anhembedded/PCS_HMI/Doc/bv h.Anh/an/1.PNG

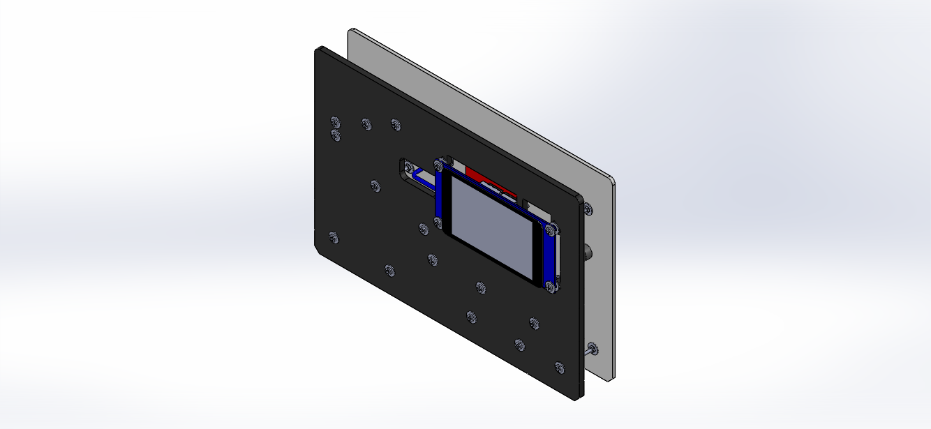
Doc/bv h.Anh/an/1.PNG
