anhembedded/PCS_HMI/Doc/bv h.Anh/an/2.PNG

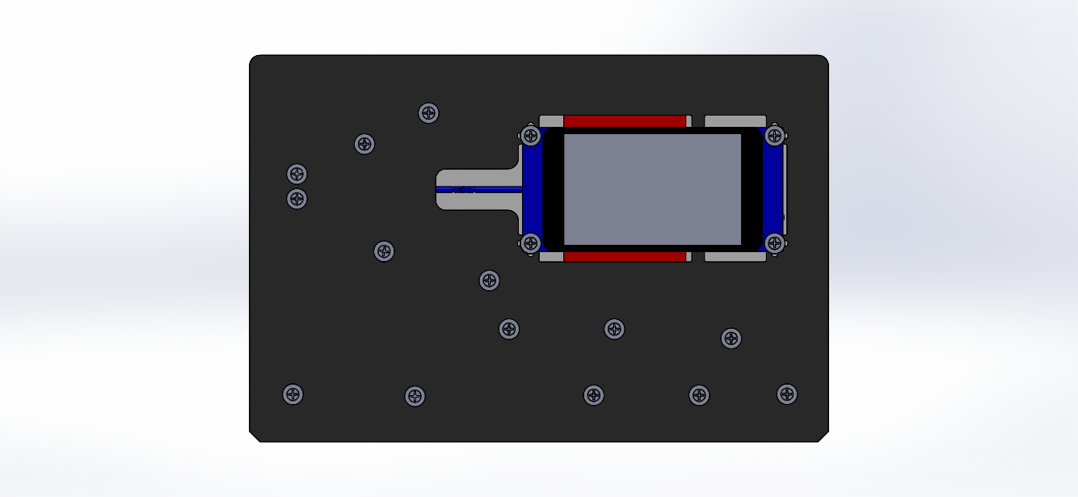
Doc/bv h.Anh/an/2.PNG
