anhembedded/PCS_HMI/Doc/bv h.Anh/an/3.PNG

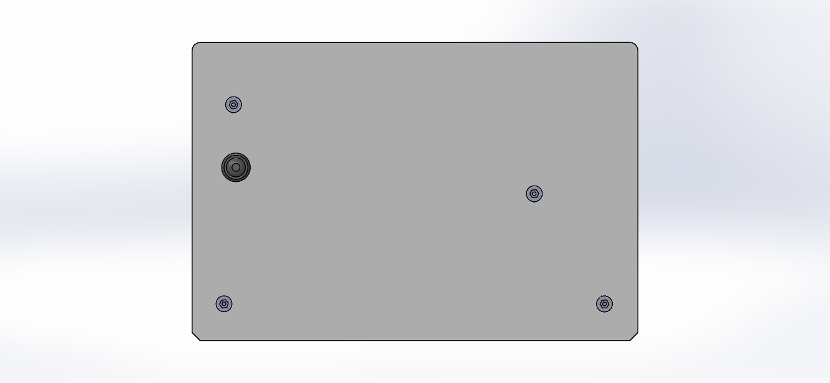
Doc/bv h.Anh/an/3.PNG
