anhembedded/PCS_HMI/Doc/bv h.Anh/an/4.PNG

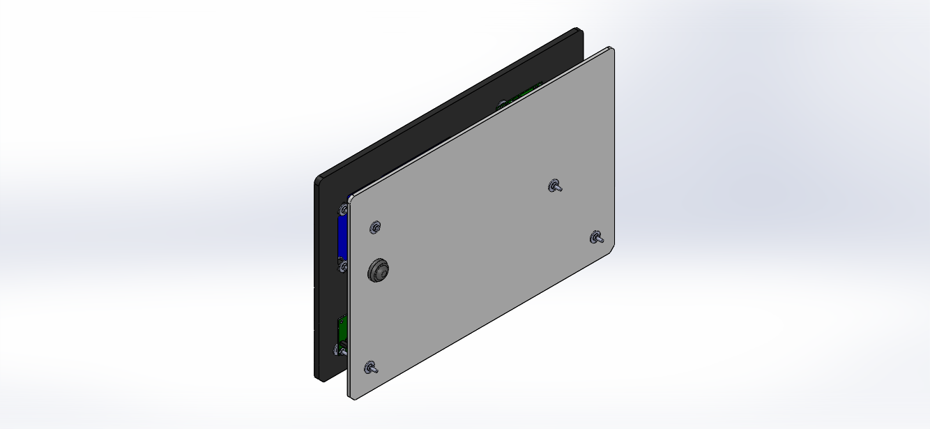
Doc/bv h.Anh/an/4.PNG
