anhembedded/PCS_HMI/Doc/bv h.Anh/an/6.PNG

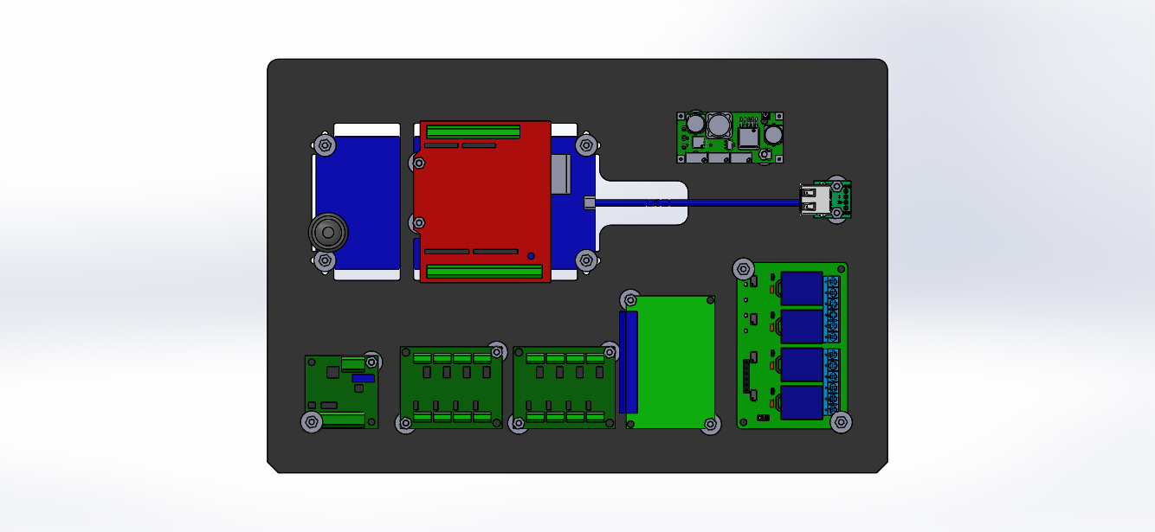
Doc/bv h.Anh/an/6.PNG
