anhembedded/PCS_HMI/Doc/bv h.Anh/arduino-uno-screw-shield-1.snapshot.9/Arduino_Uno_Screw_Shield_2020-Apr-12_04-04-14PM-000_CustomizedView19579382363.png

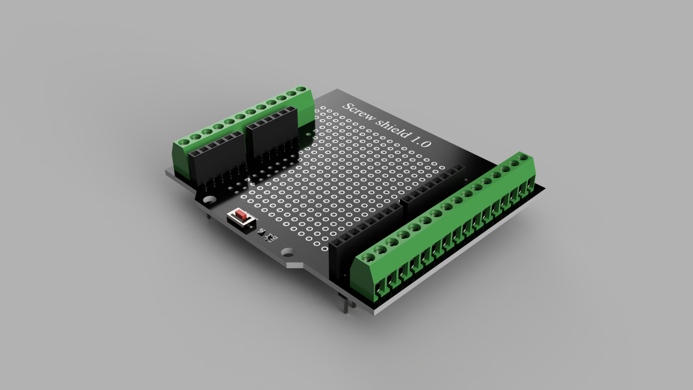
Doc/bv h.Anh/arduino-uno-screw-shield-1.snapshot.9/Arduino_Uno_Screw_Shield_2020-Apr-12_04-04-14PM-000_CustomizedView19579382363.png
