anhembedded/PCS_HMI/Doc/bv h.Anh/arduino-uno-screw-shield-1.snapshot.9/ScrewShield.jpg

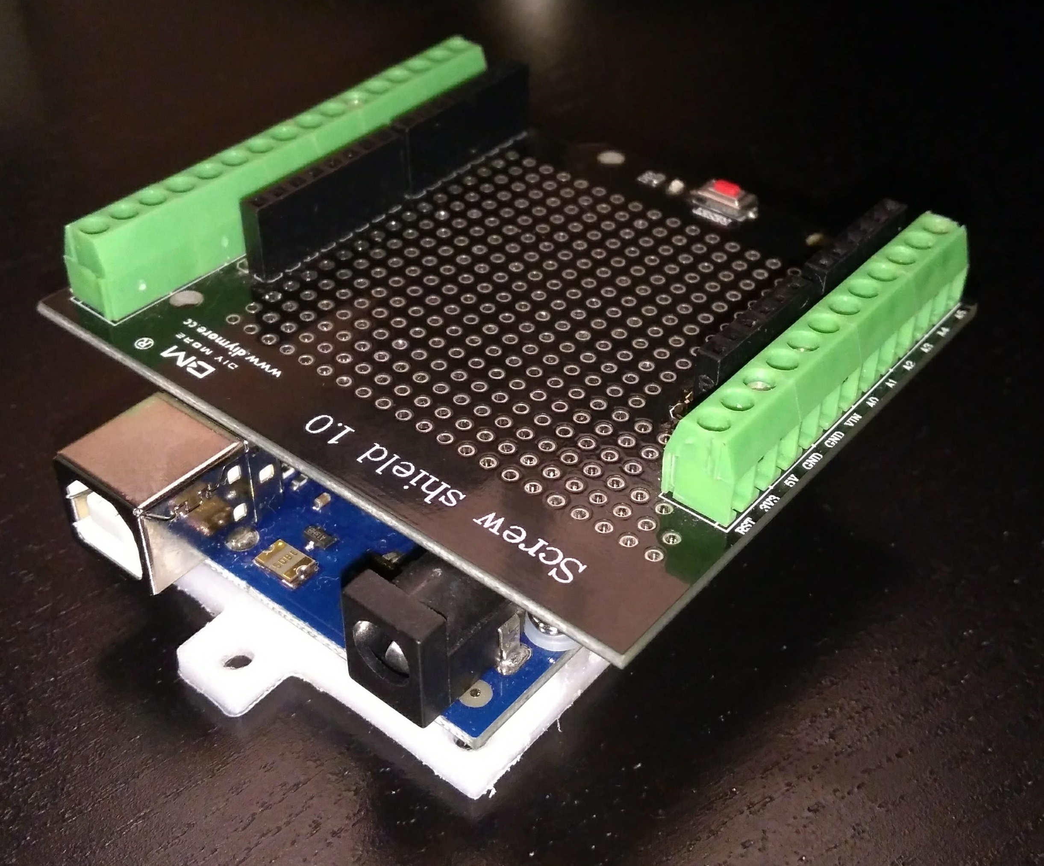
Doc/bv h.Anh/arduino-uno-screw-shield-1.snapshot.9/ScrewShield.jpg
