anhembedded/PCS_HMI/HMI_FPAC_BACKEND/TouchGFX/assets/images/__generated/alternate_theme_images_backgrounds_480x272_gradient_dark.png

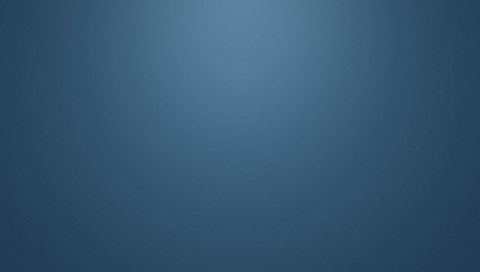
HMI_FPAC_BACKEND/TouchGFX/assets/images/__generated/alternate_theme_images_backgrounds_480x272_gradient_dark.png
