anhembedded/PCS_HMI/HMI_FPAC_BACKEND/TouchGFX/assets/images/__generated/alternate_theme_images_containers_large_wide_outlined_dark.png

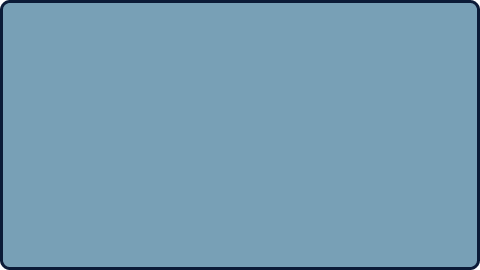
HMI_FPAC_BACKEND/TouchGFX/assets/images/__generated/alternate_theme_images_containers_large_wide_outlined_dark.png
