anhembedded/PCS_HMI/HMI_FPAC_BACKEND/TouchGFX/assets/images/__generated/alternate_theme_images_effects_800x480_shade_right_light.png

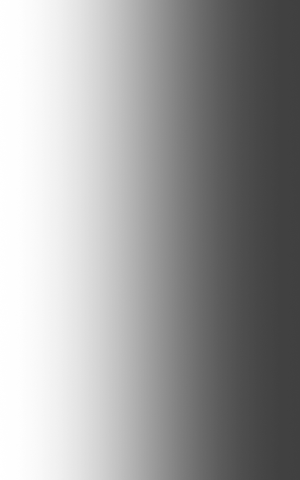
HMI_FPAC_BACKEND/TouchGFX/assets/images/__generated/alternate_theme_images_effects_800x480_shade_right_light.png
