anhembedded/PCS_HMI/Doc/bv h.Anh/mica/mica den 7mm.dxf

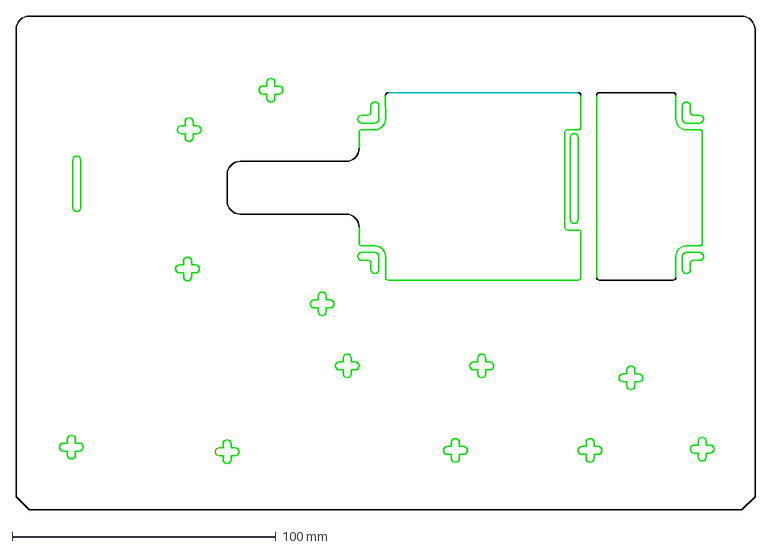
[picture p83: CAD file, 2023-07-13]
Doc/bv h.Anh/mica/mica den 7mm.dxf
280.0 x 187.0 mm
