anhembedded/PCS_HMI/Doc/bv h.Anh/ban dien/de.SLDPRT

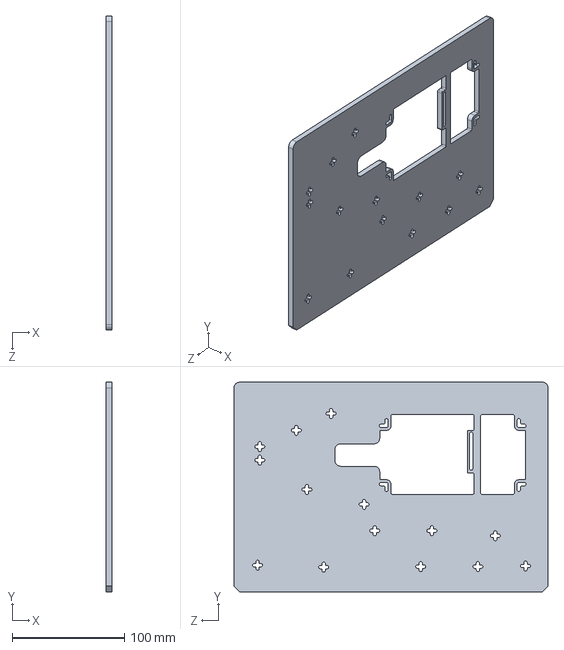
[picture p84: CAD file, 2023-07-13]
Doc/bv h.Anh/ban dien/de.SLDPRT
5.00 x 187.0 x 280.0 mm
