anhembedded/PCS_HMI/Doc/bv h.Anh/ban dien/tam lot.SLDPRT

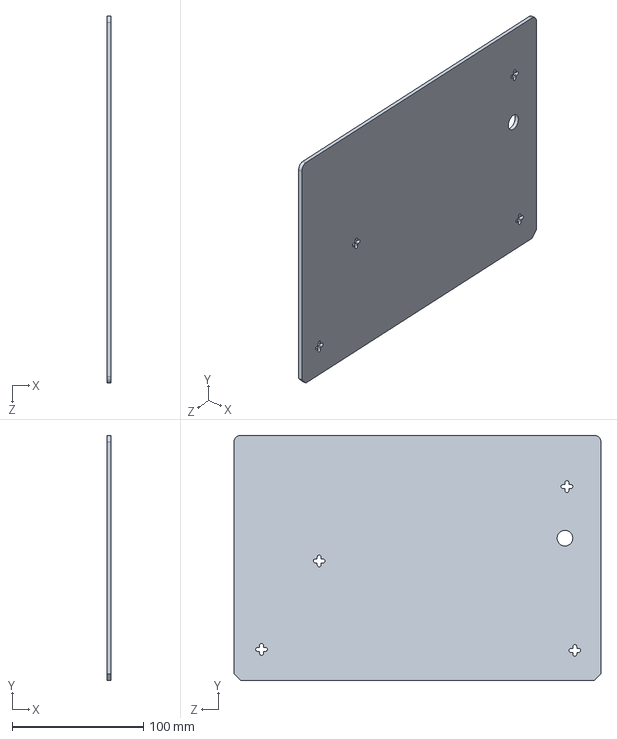
[picture p85: CAD file, 2023-07-13]
Doc/bv h.Anh/ban dien/tam lot.SLDPRT
3.00 x 187.0 x 280.0 mm
