anhembedded/PCS_HMI/Doc/bv h.Anh/ban dien/dai oc m3.SLDPRT

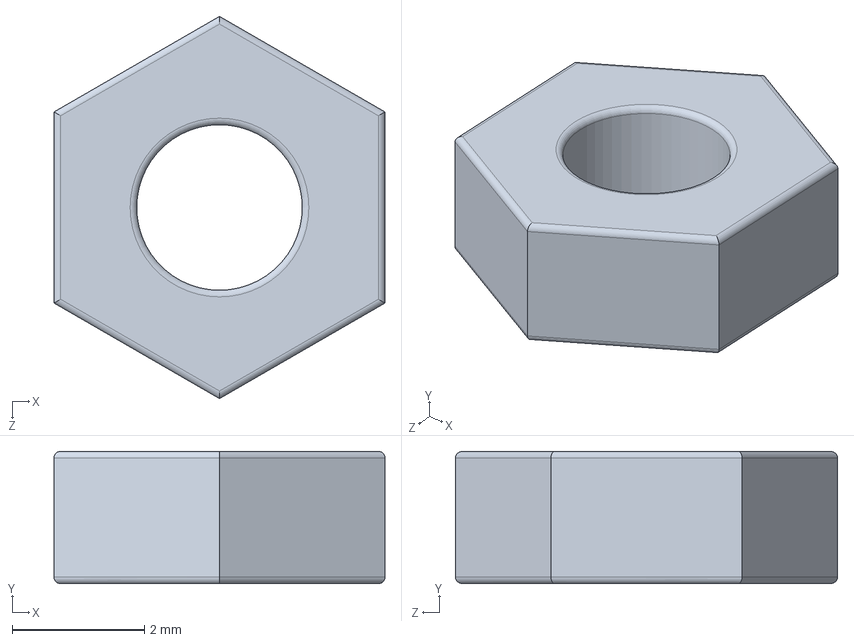
[picture p86: CAD file, 2023-07-13]
Doc/bv h.Anh/ban dien/dai oc m3.SLDPRT
5.00 x 2.00 x 5.77 mm
