anhembedded/PCS_HMI/Doc/bv h.Anh/ban dien/man hinh.SLDPRT

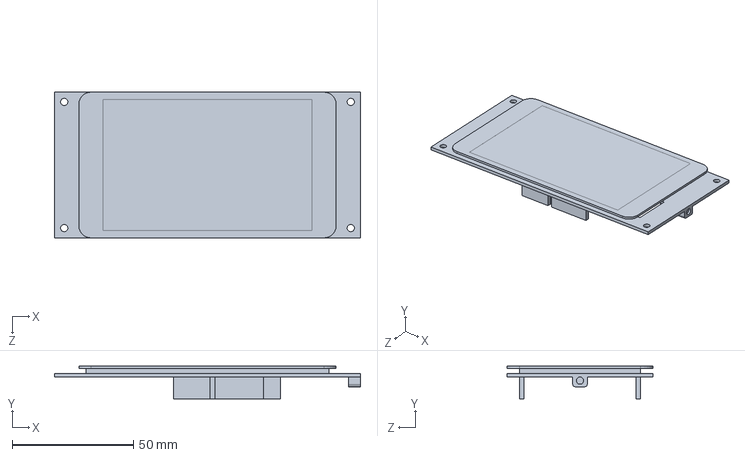
[picture p87: CAD file, 2023-07-13]
Doc/bv h.Anh/ban dien/man hinh.SLDPRT
126.0 x 13.5 x 60.0 mm
