anhembedded/PCS_HMI/Doc/bv h.Anh/ban dien/1.SLDPRT

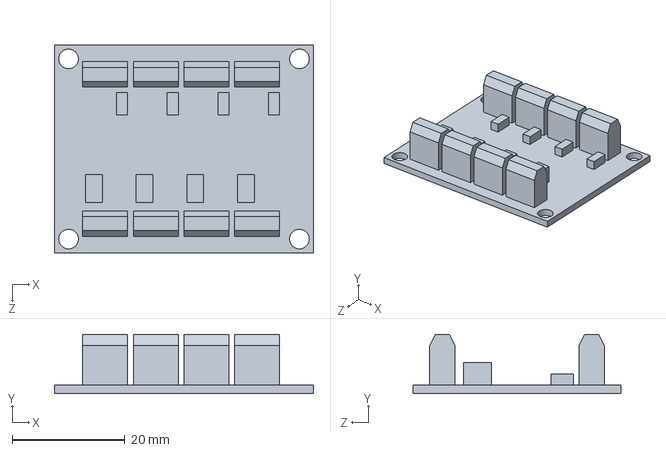
[picture p88: CAD file, 2023-07-13]
Doc/bv h.Anh/ban dien/1.SLDPRT
46.0 x 10.5 x 37.0 mm
