anhembedded/PCS_HMI/Doc/bv h.Anh/ban dien/New folder/Relay002.sldprt

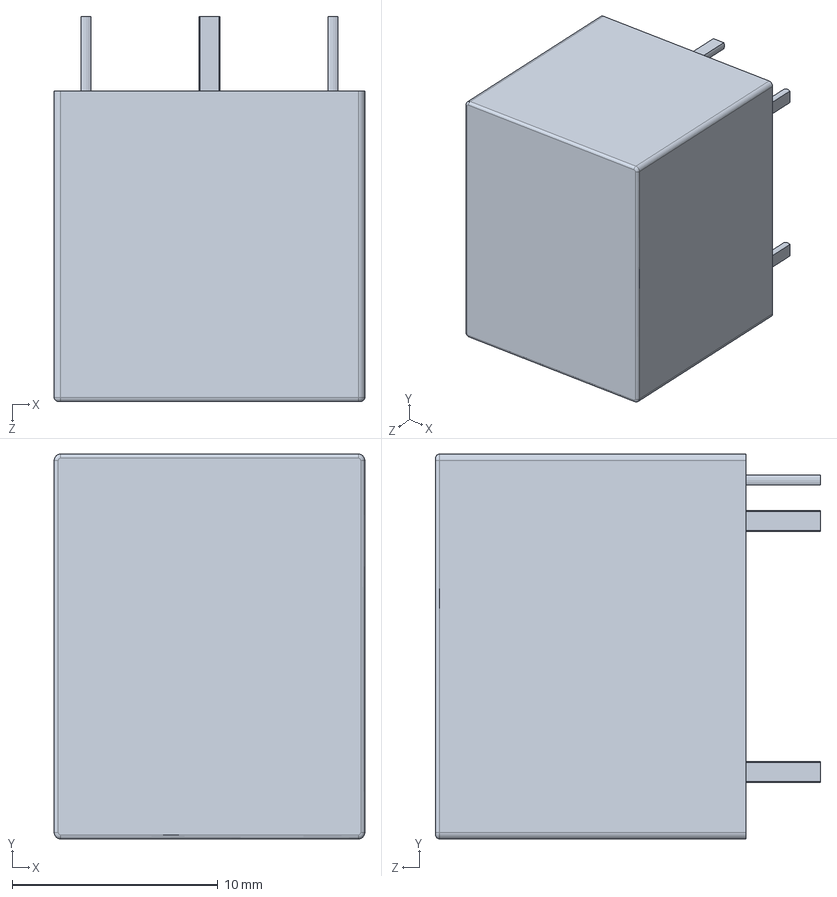
[picture p89: CAD file, 2023-07-13]
Doc/bv h.Anh/ban dien/New folder/Relay002.sldprt
15.1 x 18.7 x 18.7 mm
