anhembedded/PCS_HMI/Doc/bv h.Anh/ban dien/day cap.SLDPRT

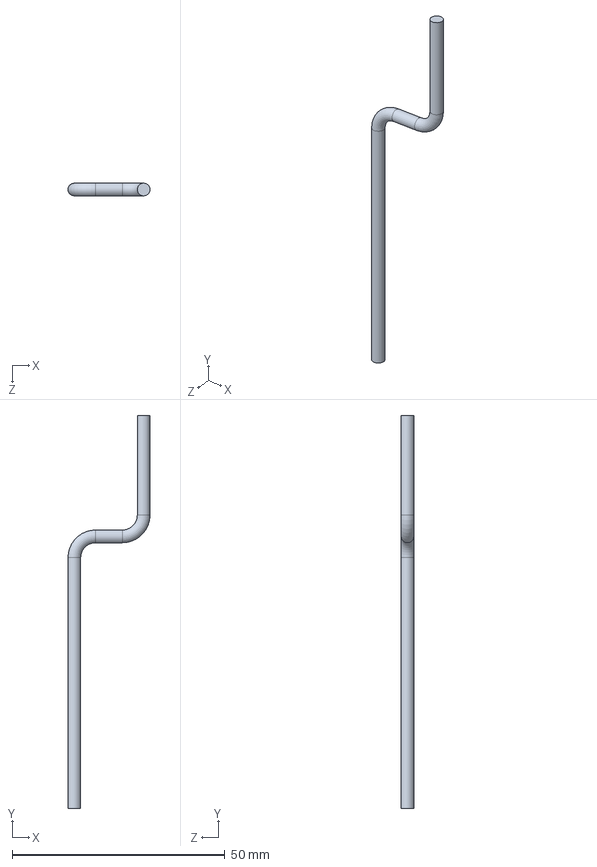
[picture p90: CAD file, 2023-07-13]
Doc/bv h.Anh/ban dien/day cap.SLDPRT
19.3 x 92.4 x 3.00 mm
