anhembedded/PCS_HMI/Doc/bv h.Anh/ban dien/m3.SLDPRT

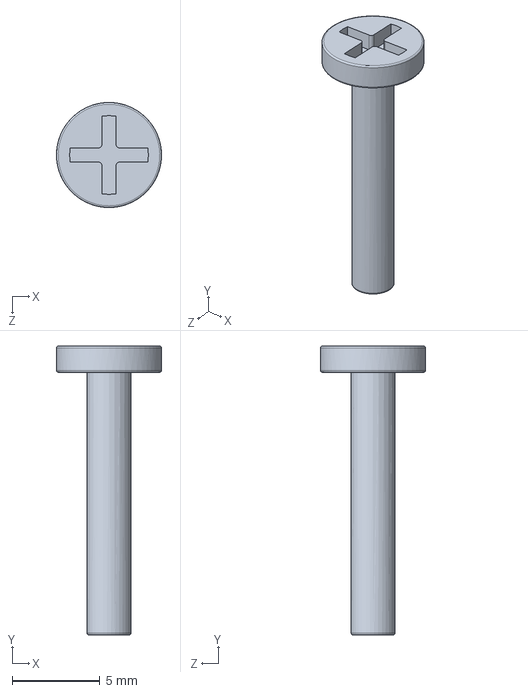
[picture p91: CAD file, 2023-07-13]
Doc/bv h.Anh/ban dien/m3.SLDPRT
6.00 x 16.5 x 6.00 mm
