anhembedded/PCS_HMI/Doc/bv h.Anh/ban dien/3.SLDPRT

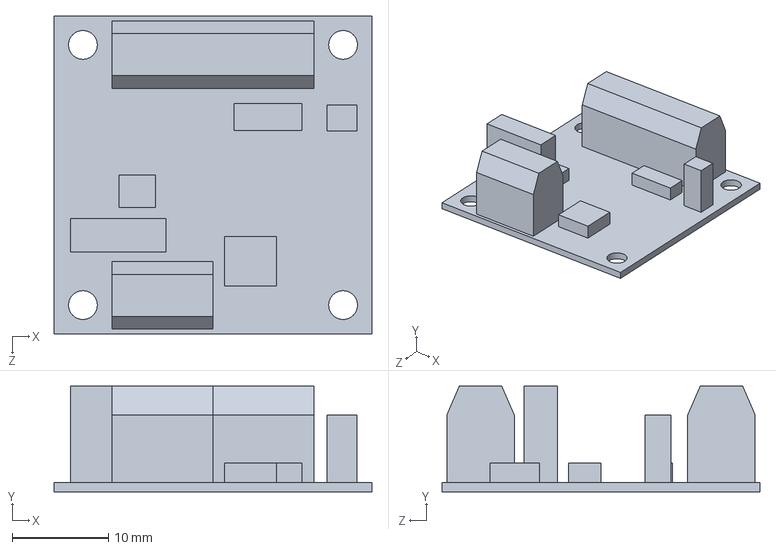
[picture p92: CAD file, 2023-07-13]
Doc/bv h.Anh/ban dien/3.SLDPRT
33.0 x 11.0 x 33.0 mm
