anhembedded/PCS_HMI/Doc/bv h.Anh/ban dien/PCB^DC-DC.sldprt

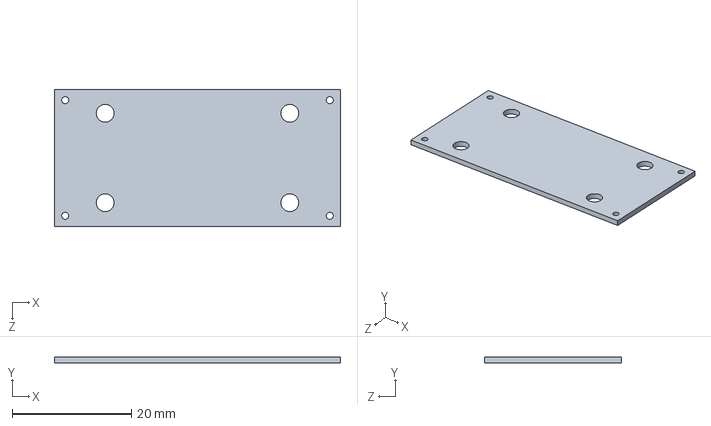
[picture p93: CAD file, 2023-07-13]
Doc/bv h.Anh/ban dien/PCB^DC-DC.sldprt
48.0 x 1.00 x 23.0 mm
