anhembedded/PCS_HMI/Doc/bv h.Anh/ban dien/usb.SLDPRT

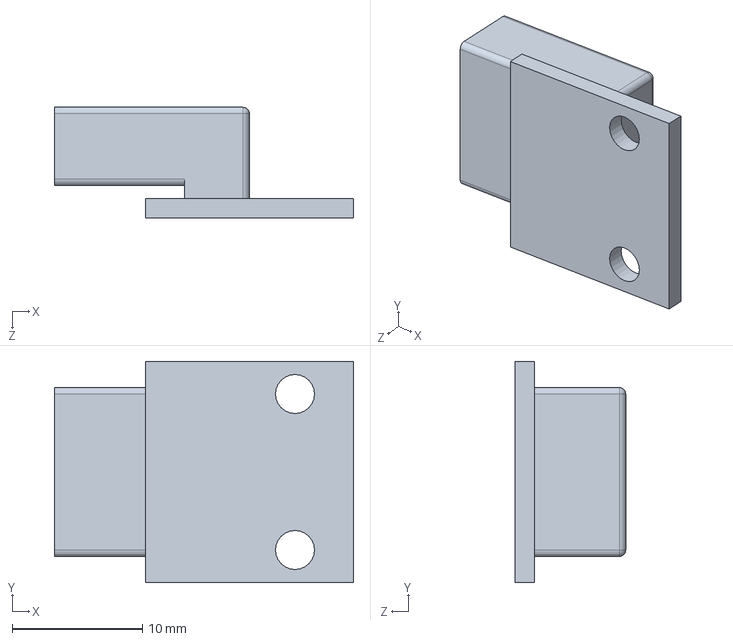
[picture p94: CAD file, 2023-07-13]
Doc/bv h.Anh/ban dien/usb.SLDPRT
23.0 x 17.0 x 8.50 mm
