anhembedded/PCS_HMI/Doc/2d model.pdf

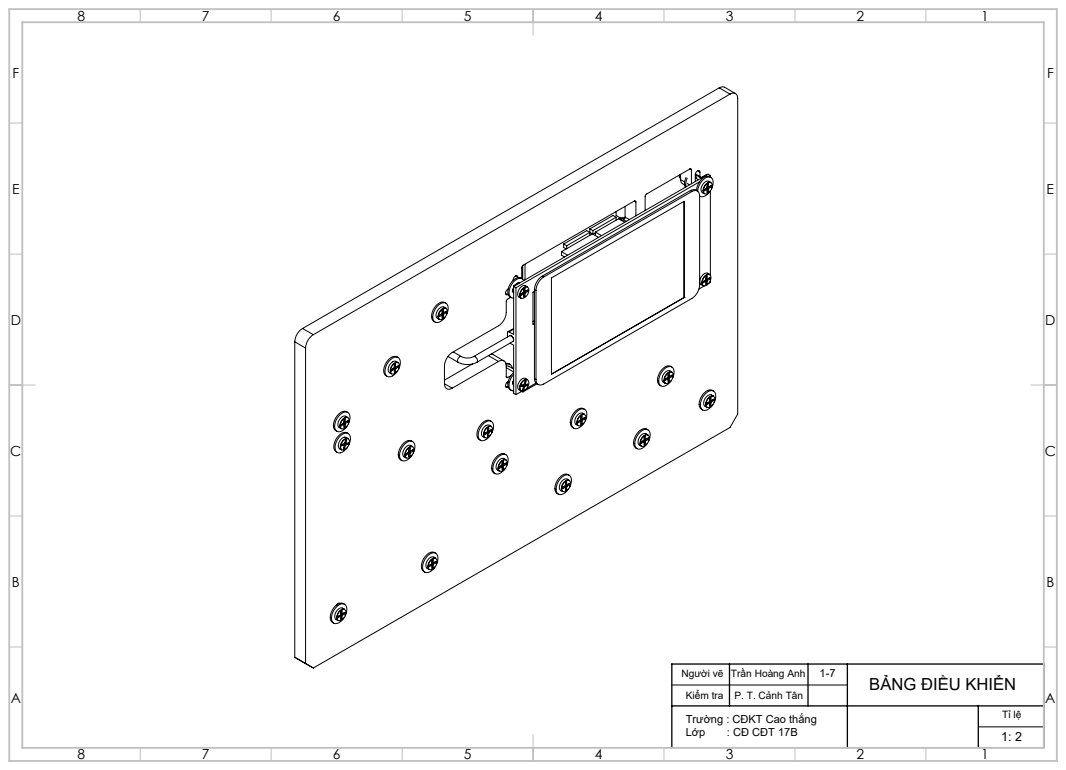
[picture p96: page 1]

Người vẽ Kiểm tra | Trần Hoàng Anh P. T. Cảnh Tân | 1-7 | BẢNG ĐIỀU KHIỂN

Trường : CĐKT Cao thắng Lớp : CĐ CĐT 17B | | Tỉ lệ 1: 2

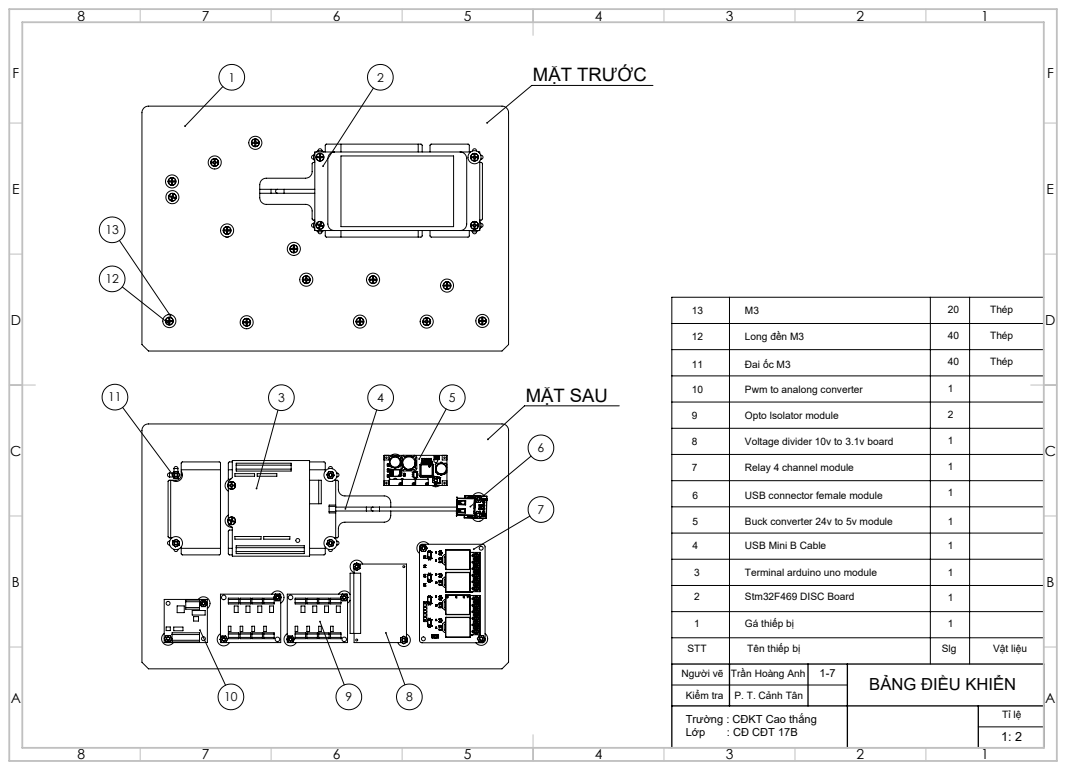
[picture p97: page 2]
MẶT SAU; MẶT TRƯỚC; Lớp; : CĐ CĐT 17B

13 | M3 | 20 | Thép
12 | Long đền M3 | 40 | Thép
11 | Đai ốc M3 | 40 | Thép
10 | Pwm to analong converter | 1
9 | Opto lsolator module | 2
8 | Voltage divider 10v to 3.1v board | 1
7 | Relay 4 channel module | 1
6 | USB connector female module | 1

5 | Buck converter 24v to 5v module | 1
4 | USB Mini B Cable | 1

3 | Terminal arduino uno module | 1
2 | Stm32F469 DISC Board | 1

1 | Gá thiếp bị | 1
STT | Tên thiếp bị | Slg | Vật liệu
Người vẽ | Trần Hoàng Anh | 1-7 | BẢNG ĐIỀU KHIỂN
Kiểm tra | P. T. Cảnh Tân

Trường : CĐKT Cao thắng

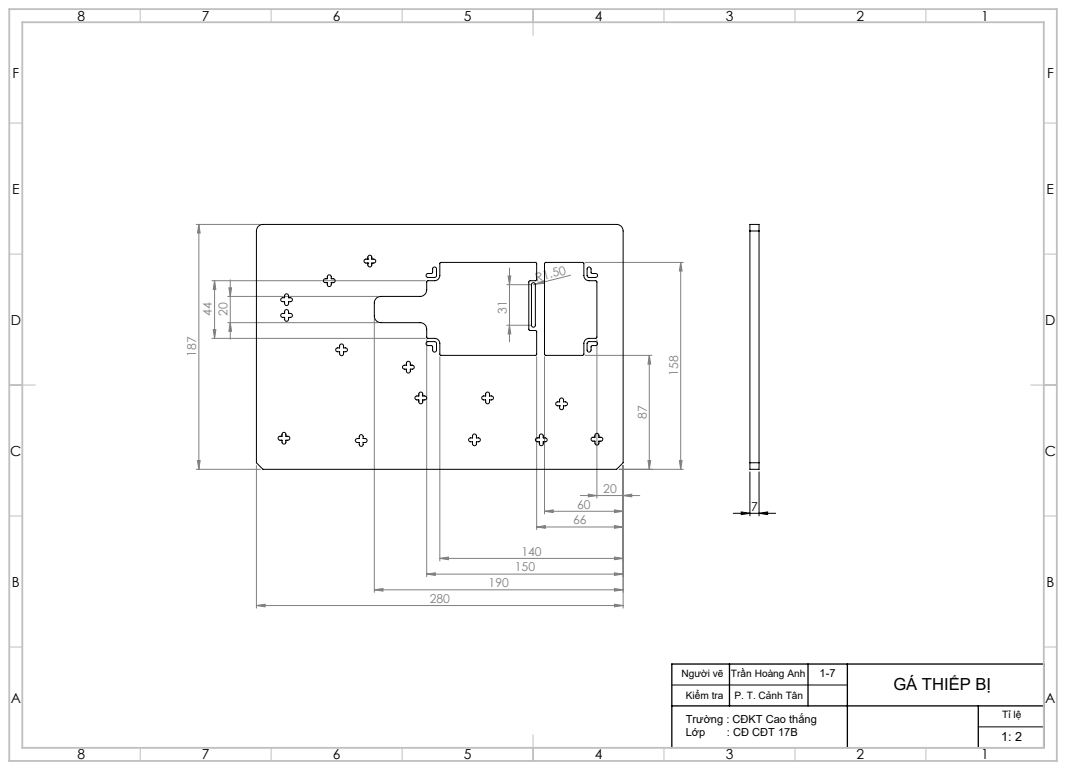
[picture p98: page 3]

Người vẽ Kiểm tra | Trần Hoàng Anh P. T. Cảnh Tân | 1-7 | GÁ THIẾP BỊ

Trường : CĐKT Cao thắng Lớp : CĐ CĐT 17B | | Tỉ lệ 1: 2

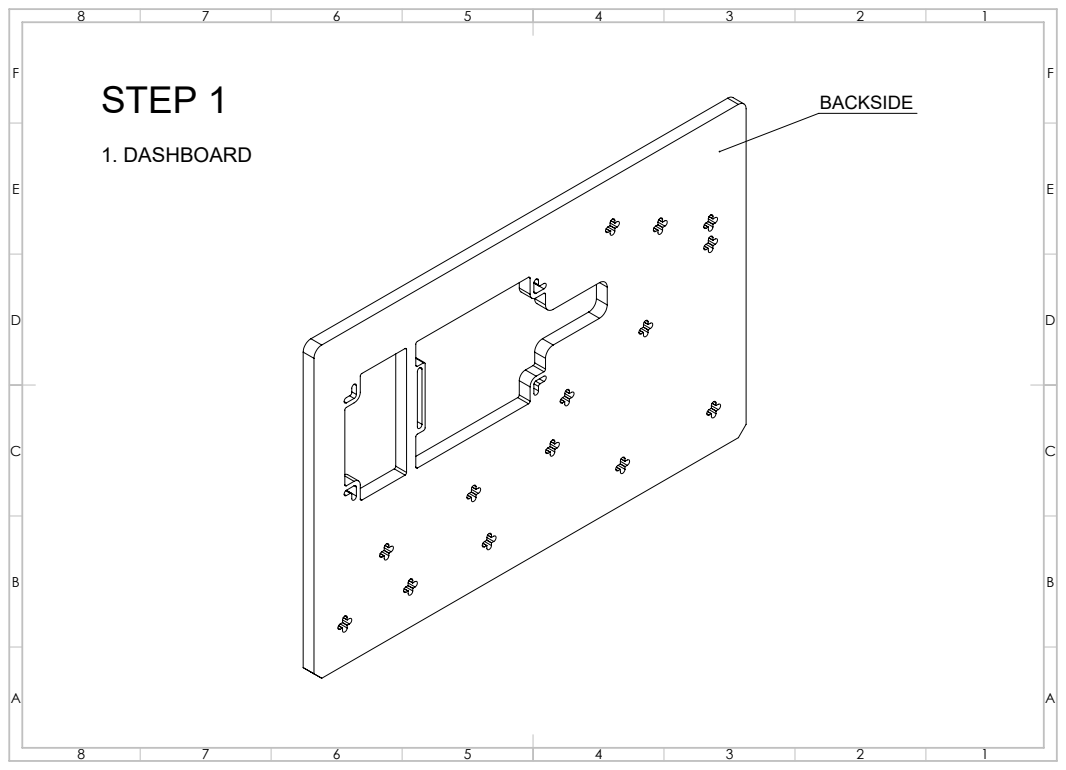
[picture p99: page 4]
STEP 1 BACKSIDE; 1. DASHBOARD

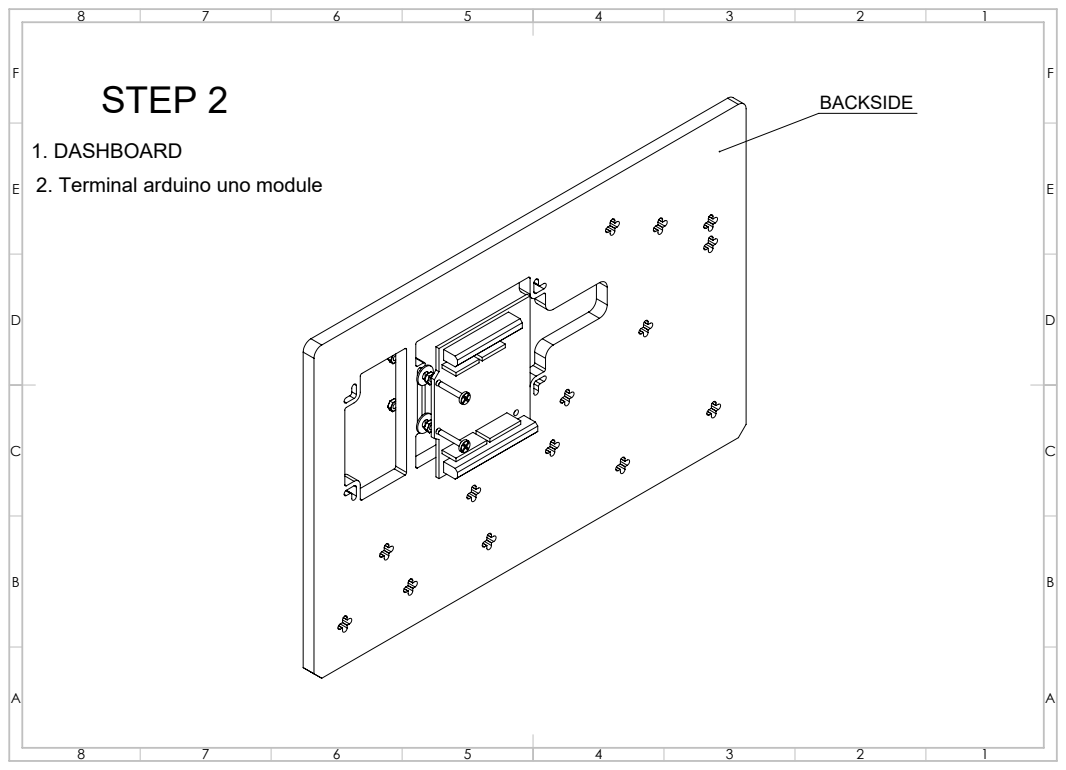
[picture p100: page 5]
STEP 2 BACKSIDE

1. DASHBOARD
2. Terminal arduino uno module

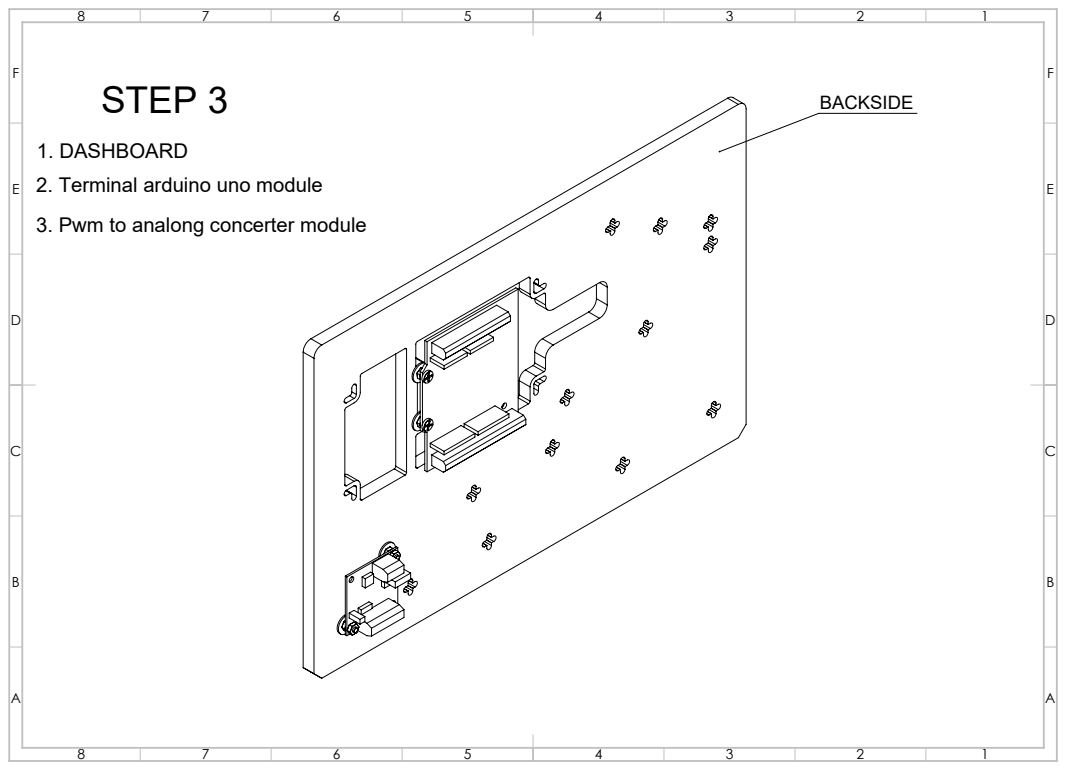
[picture p101: page 6]
STEP 3 BACKSIDE

1. DASHBOARD
2. Terminal arduino uno module
3. Pwm to analong concerter module

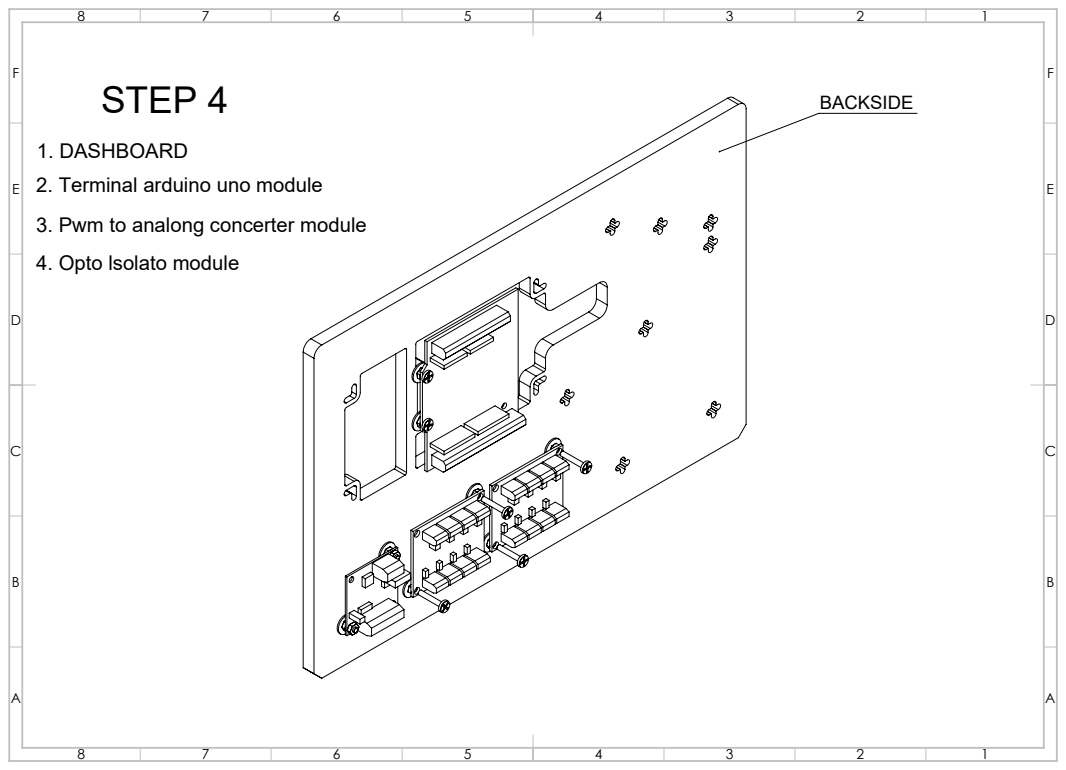
[picture p102: page 7]
STEP 4 BACKSIDE

1. DASHBOARD
2. Terminal arduino uno module
3. Pwm to analong concerter module
4. Opto lsolato module

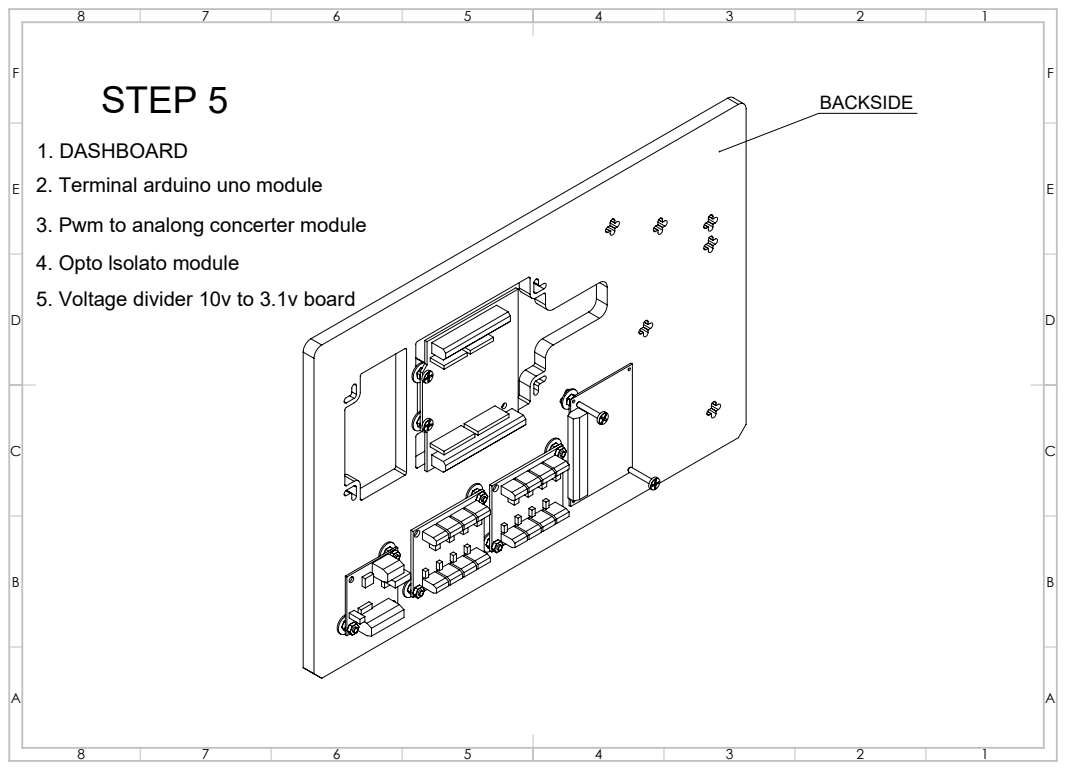
[picture p103: page 8]
STEP 5 BACKSIDE

1. DASHBOARD
2. Terminal arduino uno module
3. Pwm to analong concerter module
4. Opto lsolato module
5. Voltage divider 10v to 3.1v board

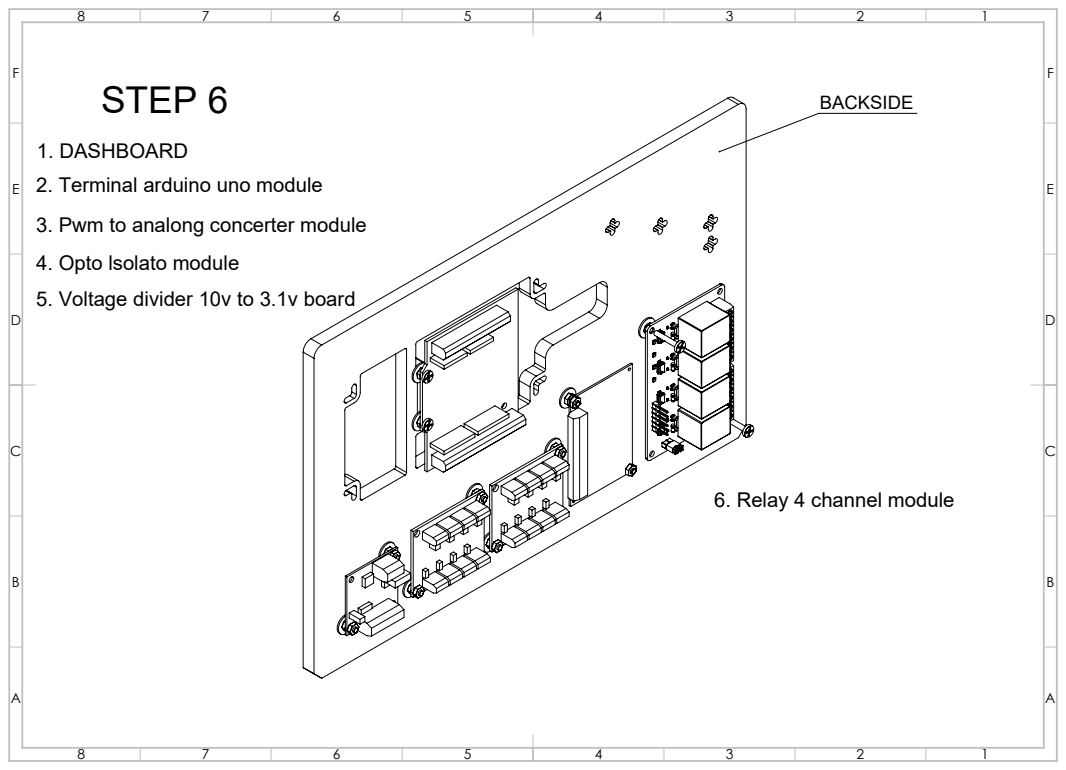
[picture p104: page 9]
STEP 6 BACKSIDE

1. DASHBOARD
2. Terminal arduino uno module
3. Pwm to analong concerter module
4. Opto lsolato module
5. Voltage divider 10v to 3.1v board

6. Relay 4 channel module

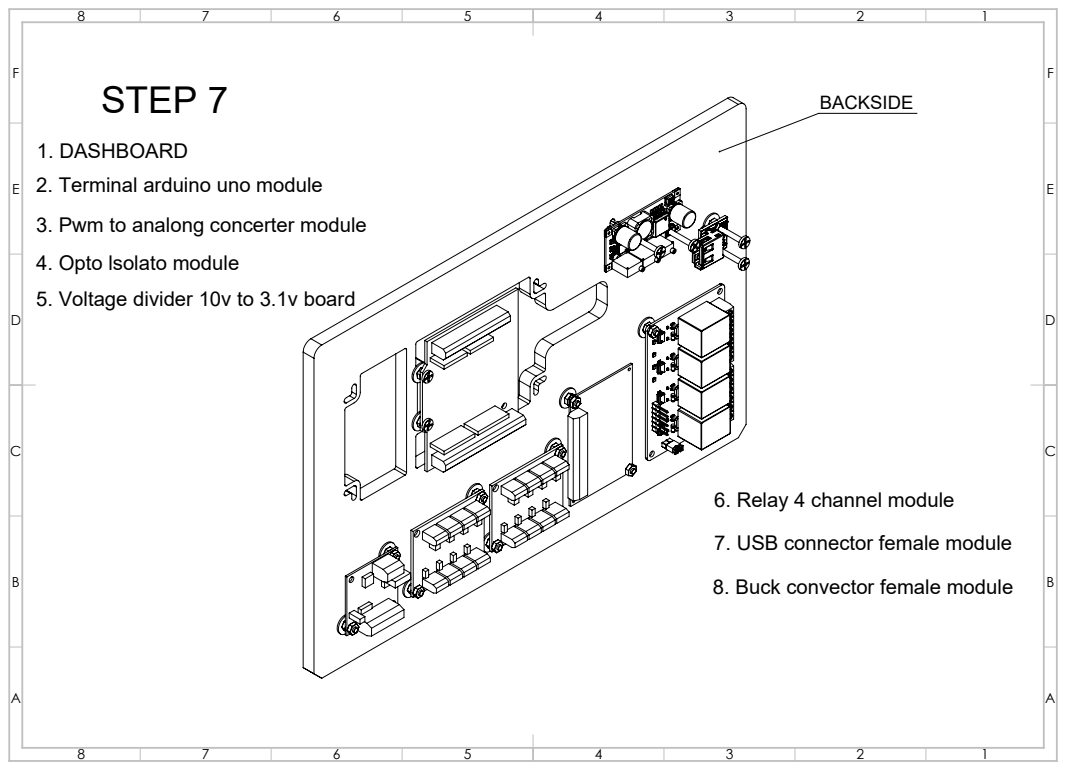
[picture p105: page 10]
STEP 7 BACKSIDE

1. DASHBOARD
2. Terminal arduino uno module
3. Pwm to analong concerter module
4. Opto lsolato module
5. Voltage divider 10v to 3.1v board

6. Relay 4 channel module
7. USB connector female module
8. Buck convector female module

# Front STEP 8

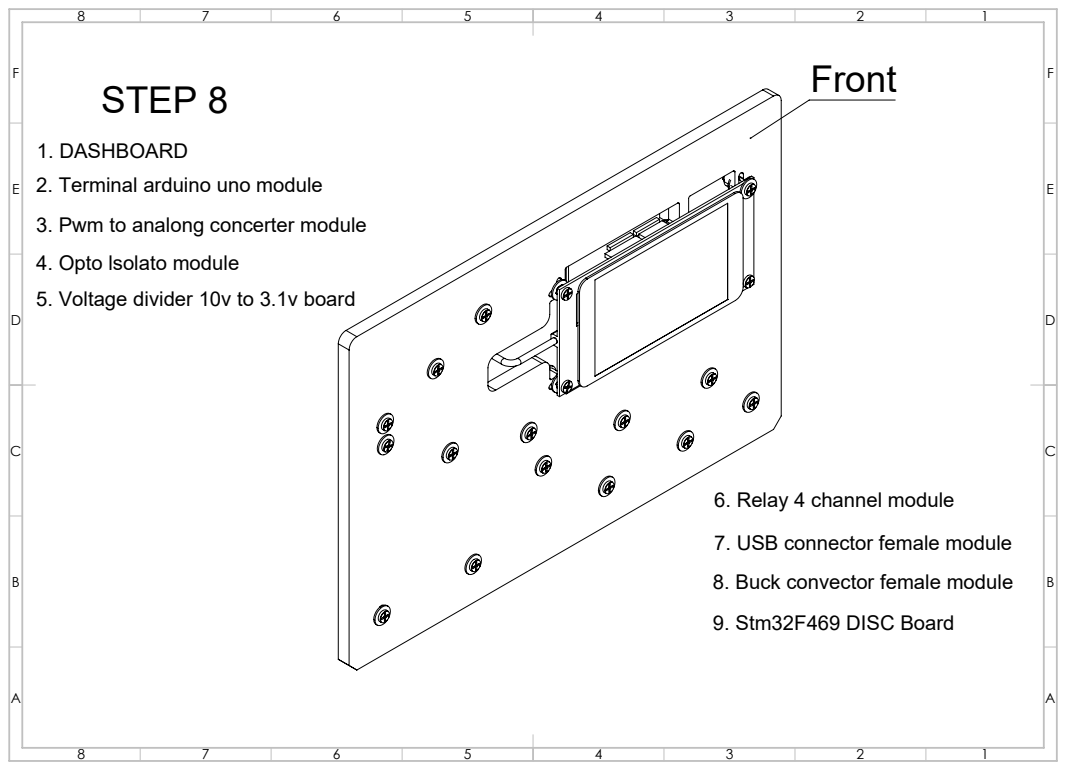
[picture p106: page 11]

1. DASHBOARD
2. Terminal arduino uno module
3. Pwm to analong concerter module
4. Opto lsolato module
5. Voltage divider 10v to 3.1v board

6. Relay 4 channel module
7. USB connector female module
8. Buck convector female module
9. Stm32F469 DISC Board

# Front STEP 9

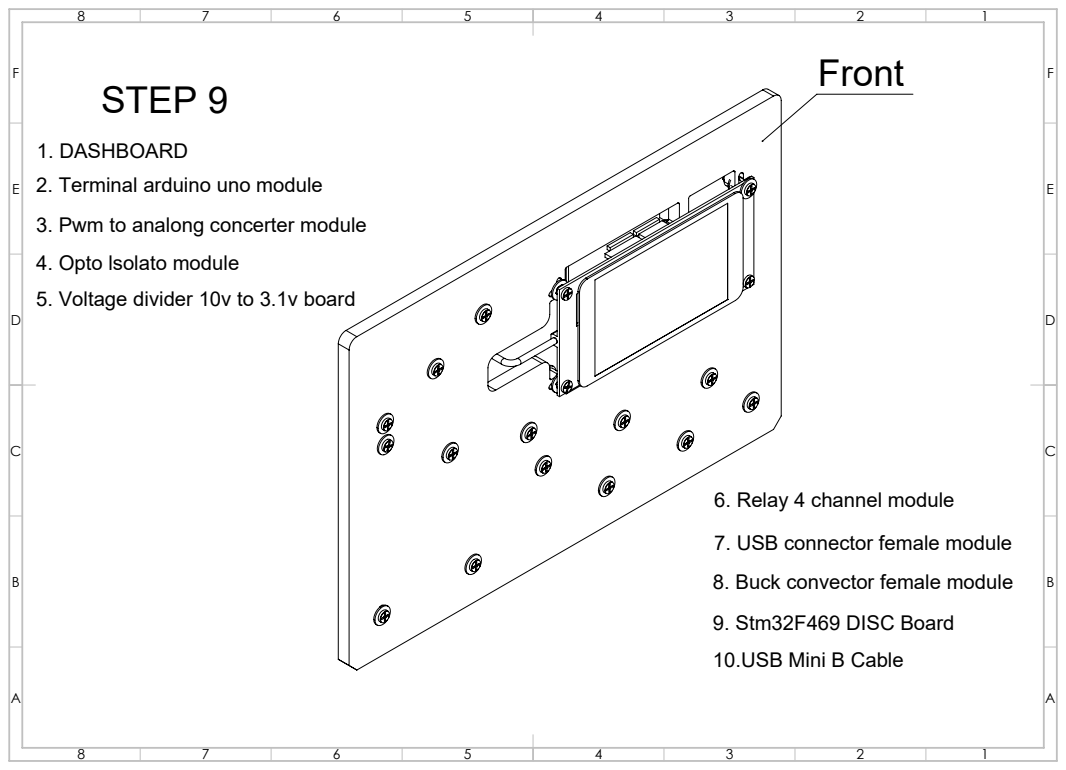
[picture p107: page 12]

1. DASHBOARD
2. Terminal arduino uno module
3. Pwm to analong concerter module
4. Opto lsolato module
5. Voltage divider 10v to 3.1v board

6. Relay 4 channel module
7. USB connector female module
8. Buck convector female module
9. Stm32F469 DISC Board
10.USB Mini B Cable
