anhembedded/PCS_HMI/Doc/PCS_Signal_converter_Hoang_Anh_2023.pdf

in1

v1

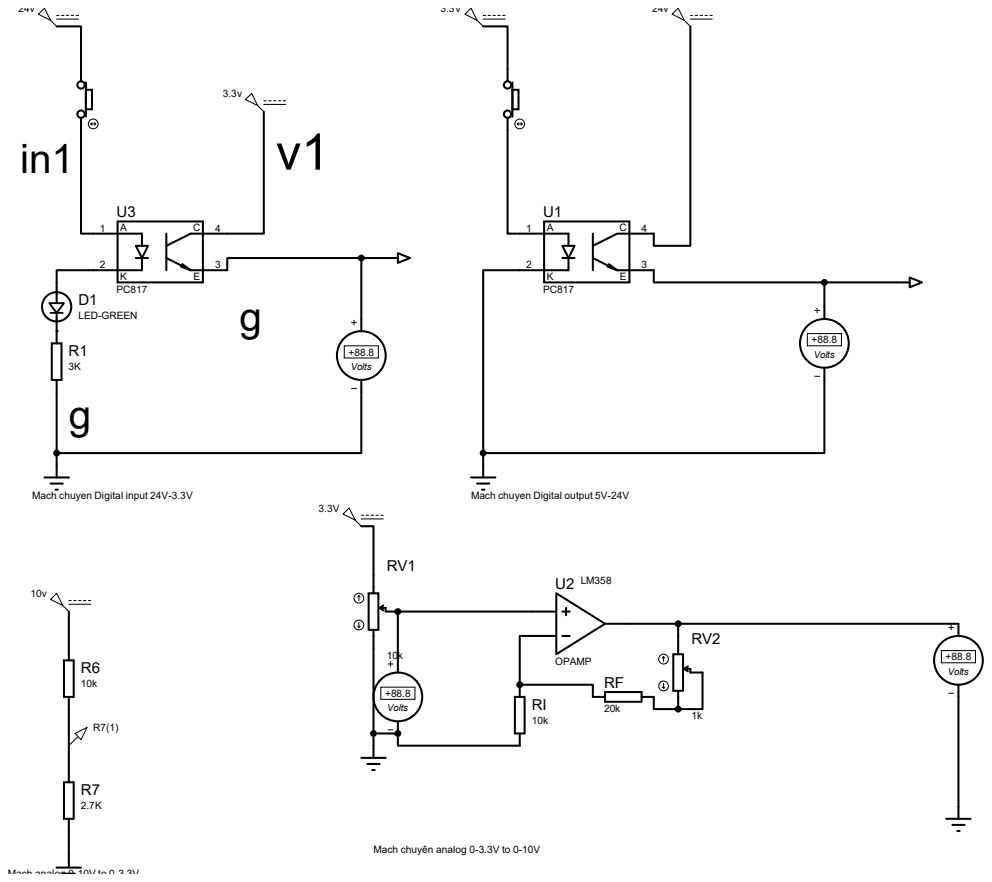
[picture p108: page 1]
Mach chuyen Digital input 24V-3.3V; Mach chuyen Digital output 5V-24V; LED-GREEN; +88.8 Volts; OPAMP; Volts

Mach chuyên analog 0-3.3V to 0-10V

Mach analog 0-10V to 0-3.3V
