anhembedded/PCS_HMI/Doc/Bản vẽ điện final.pdf

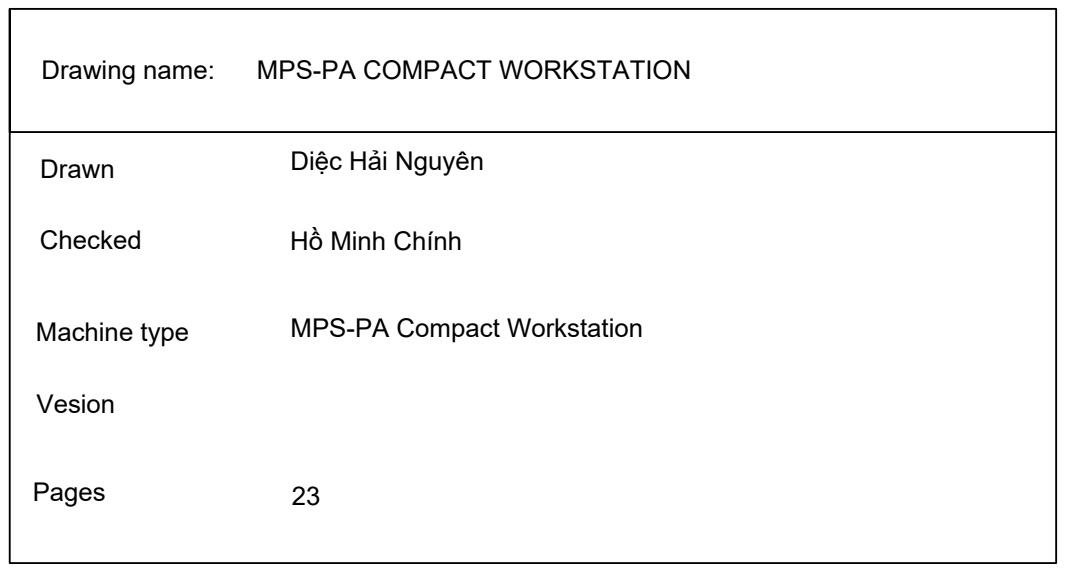
[picture p109: page 1]
Drawing name:; Machine type; Tên máy:; Trang kế: 2

MPS-PA COMPACT WORKSTATION

Diệc Hải Nguyên

Hồ Minh Chính

MPS-PA Compact Workstation

Người vẽ | Diệc Hải Nguyên | 28/06/21 | Tên bản vẽ: TRANG BÌA

Người kiểm tra | Hồ Minh Chính

Trường: Cao Đẳng Kỹ Thuật Cao Thắng
Bộ môn: Cơ điện tử
Lớp: CĐ CĐT 18A

Trang: 1

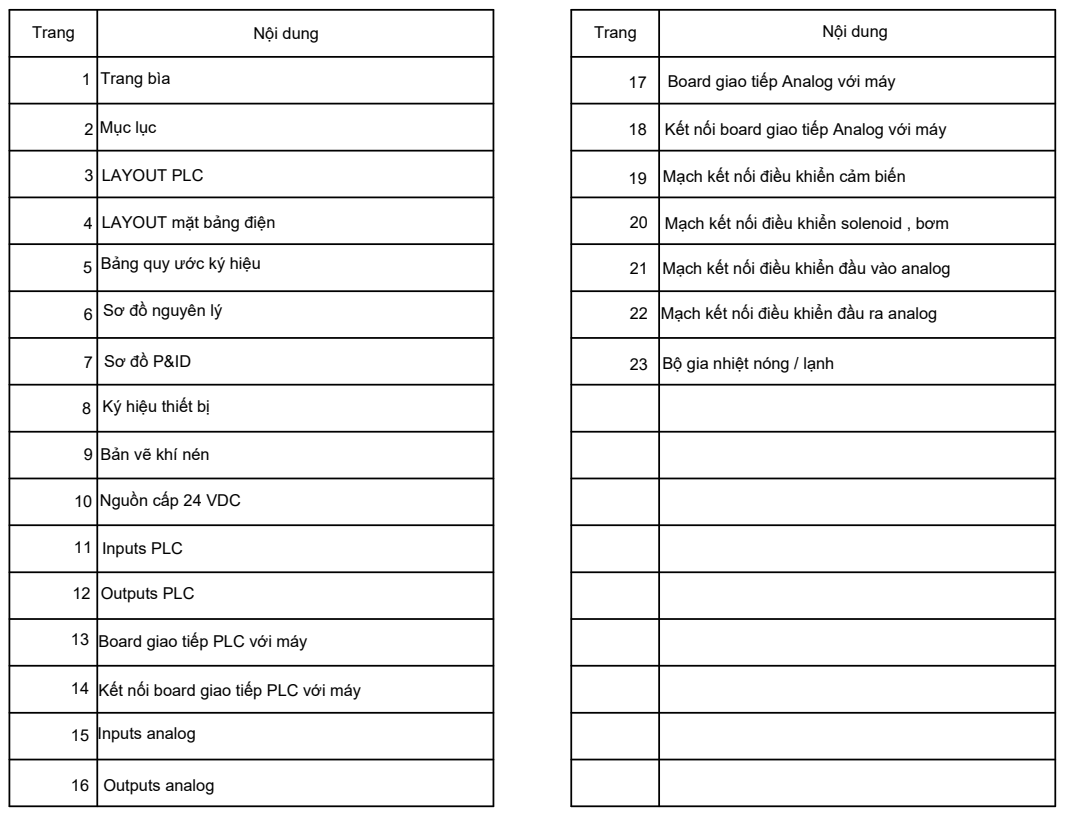
[picture p110: page 2]
Trang bìa; Mục lục; LAYOUT PLC; Trang; Nội dung; Tên máy:; Trang: 2; Trang kế: 3; Mạch kết nối điều khiển đầu ra analog

Board giao tiếp Analog với máy

Kết nối board giao tiếp Analog với máy

Mạch kết nối điều khiển cảm biến

LAYOUT mặt bảng điện

Mạch kết nối điều khiển solenoid , bơm

Bảng quy ước ký hiệu

Mạch kết nối điều khiển đầu vào analog

Sơ đồ nguyên lý

Bộ gia nhiệt nóng / lạnh

8 | Ký hiệu thiết bị

9 | Bản vẽ khí nén

10 | Nguồn cấp 24 VDC

11 | Inputs PLC

12 | Outputs PLC

13 | Board giao tiếp PLC với máy

14 | Kết nối board giao tiếp PLC với máy

15 | Inputs analog

16 | Outputs analog

Người vẽ | Diệc Hải Nguyên | 28/06/21 | Tên bản vẽ: MỤC LỤC

Người kiểm tra | Hồ Minh Chính

Trường: Cao Đẳng Kỹ Thuật Cao Thắng
Bộ môn: Cơ điện tử
Lớp: CĐ CĐT 18A

MPS-PA Compact Workstation

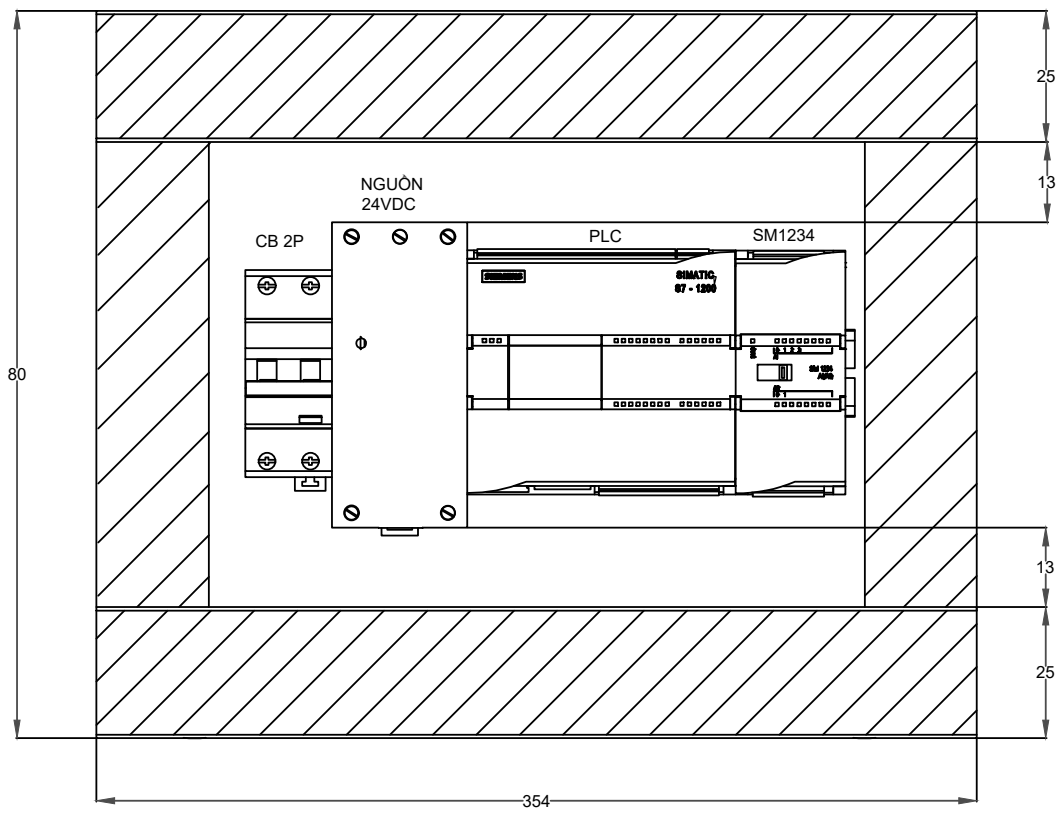
[picture p111: page 3]
Tên máy:; Trang: 3; Trang kế: 4

NGUỒN 24VDC | | 13

PLC SM1234 CB 2P

Người vẽ | Diệc Hải Nguyên | 28/06/21 | Tên bản vẽ: LAYOUT PLC

Người kiểm tra | Hồ Minh Chính

Trường: Cao Đẳng Kỹ Thuật Cao Thắng
Bộ môn: Cơ điện tử
Lớp: CĐ CĐT 18A

MPS-PA Compact Workstation

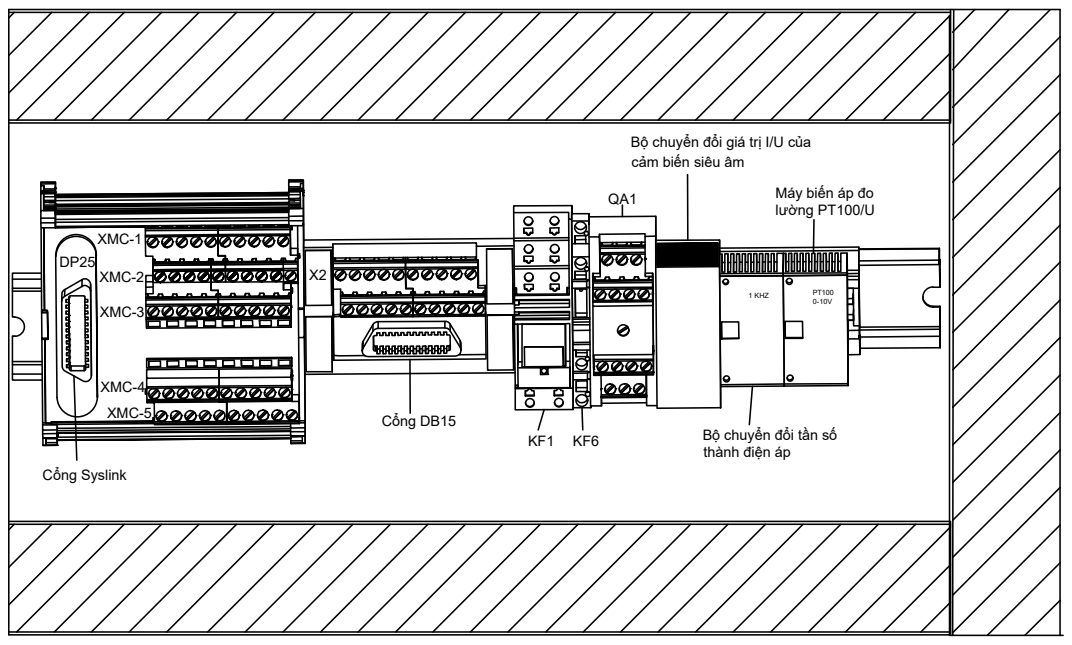
[picture p112: page 4]
Tên máy:; Trang: 4; Trang kế: 5; Cổng Syslink; Cổng DB15; 1 KHZ

Bộ chuyển đổi giá trị I/U của
cảm biến siêu âm

Máy biến áp đo
lường PT100/U

Bộ chuyển đổi tần số
thành điện áp

Người vẽ | Diệc Hải Nguyên | 28/06/21 | Tên bản vẽ: LAYOUT MẶT BẢNG ĐIỆN

Người kiểm tra | Hồ Minh Chính

Trường: Cao Đẳng Kỹ Thuật Cao Thắng
Bộ môn: Cơ điện tử
Lớp: CĐ CĐT 18A

MPS-PA Compact Workstation

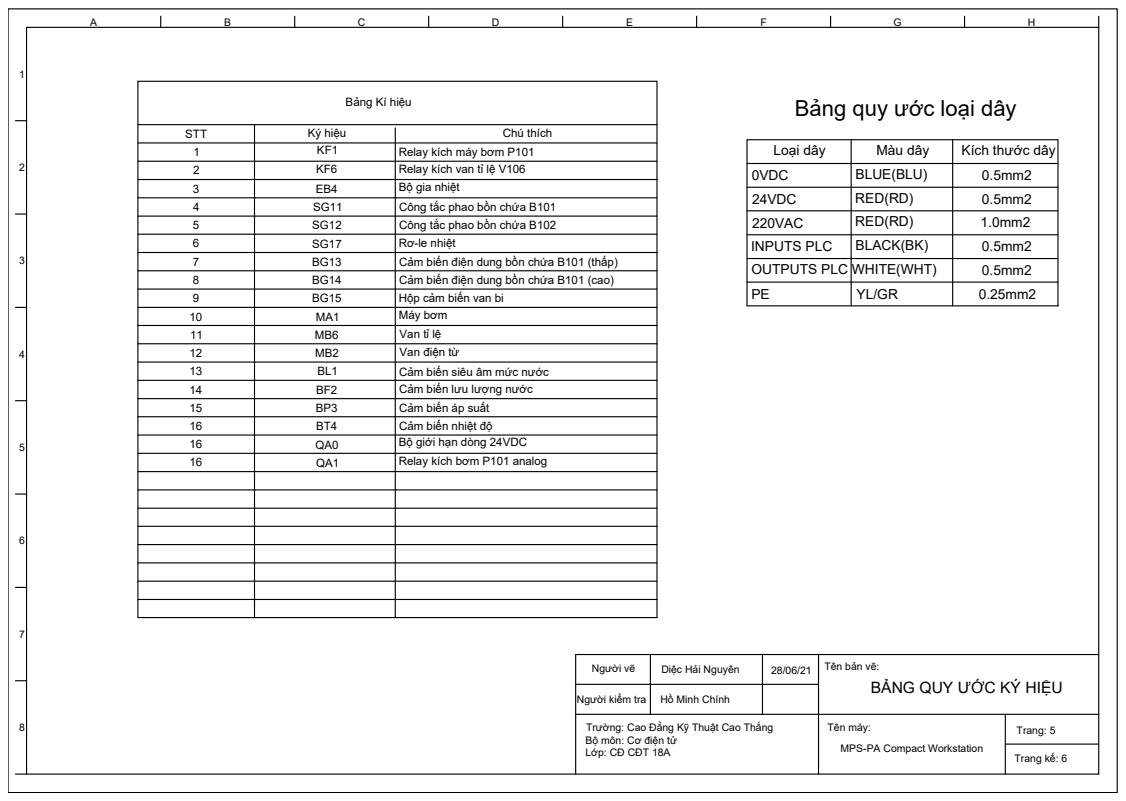
[picture p113: page 5]
Tên máy:; Trang: 5; Trang kế: 6; Loại dây; INPUTS PLC; Màu dây; STT; Ký hiệu; Chú thích; Rơ-le nhiệt

Bảng Kí hiệu

Bảng quy ước loại dây

Relay kích máy bơm P101
Relay kích van tỉ lệ V106

Kích thước dây

3 | EB4 | Bộ gia nhiệt
4 | SG11 | Công tắc phao bồn chứa B101
5 | SG12 | Công tắc phao bồn chứa B102

24VDC | RED(RD) | 0.5mm2
220VAC | RED(RD) | 1.0mm2

7 | BG13 | Cảm biến điện dung bồn chứa B101 (thấp)
8 | BG14 | Cảm biến điện dung bồn chứa B101 (cao)
9 | BG15 | Hộp cảm biến van bi
10 | MA1 | Máy bơm
11 | MB6 | Van tỉ lệ
12 | MB2 | Van điện từ
13 | BL1 | Cảm biến siêu âm mức nước
14 | BF2 | Cảm biến lưu lượng nước
15 | BP3 | Cảm biến áp suất
16 | BT4 | Cảm biến nhiệt độ
16 | QA0 | Bộ giới hạn dòng 24VDC
16 | QA1 | Relay kích bơm P101 analog

OUTPUTS PLC WHITE(WHT) | | 0.5mm2

Người vẽ | Diệc Hải Nguyên | 28/06/21 | Tên bản vẽ: BẢNG QUY ƯỚC KÝ HIỆU
Người kiểm tra | Hồ Minh Chính

Trường: Cao Đẳng Kỹ Thuật Cao Thắng
Bộ môn: Cơ điện tử
Lớp: CĐ CĐT 18A

MPS-PA Compact Workstation

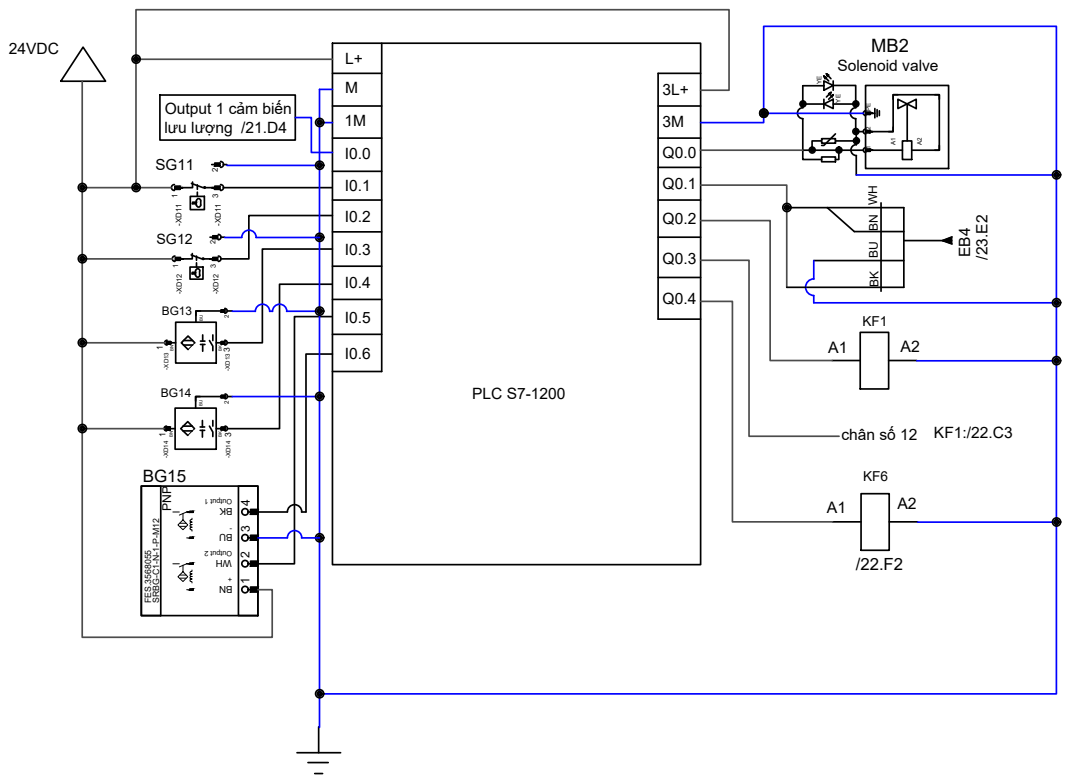
[picture p114: page 6]
Tên máy:; Trang: 6; PLC S7-1200; 24VDC; Solenoid valve 2 PE A1 A2; chân số 12; lưu lượng /21.D4

Output 1 cảm biến

1 2 3 4 FES.3568055 SRBG-C1-N-1-P-M12 PNP

Người vẽ | Diệc Hải Nguyên | 28/06/21 | Tên bản vẽ: SƠ ĐỒ NGUYÊN LÝ

Người kiểm tra | Hồ Minh Chính

Trường: Cao Đẳng Kỹ Thuật Cao Thắng
Bộ môn: Cơ điện tử
Lớp: CĐ CĐT 18A

Trang kế: 7 MPS-PA Compact Workstation

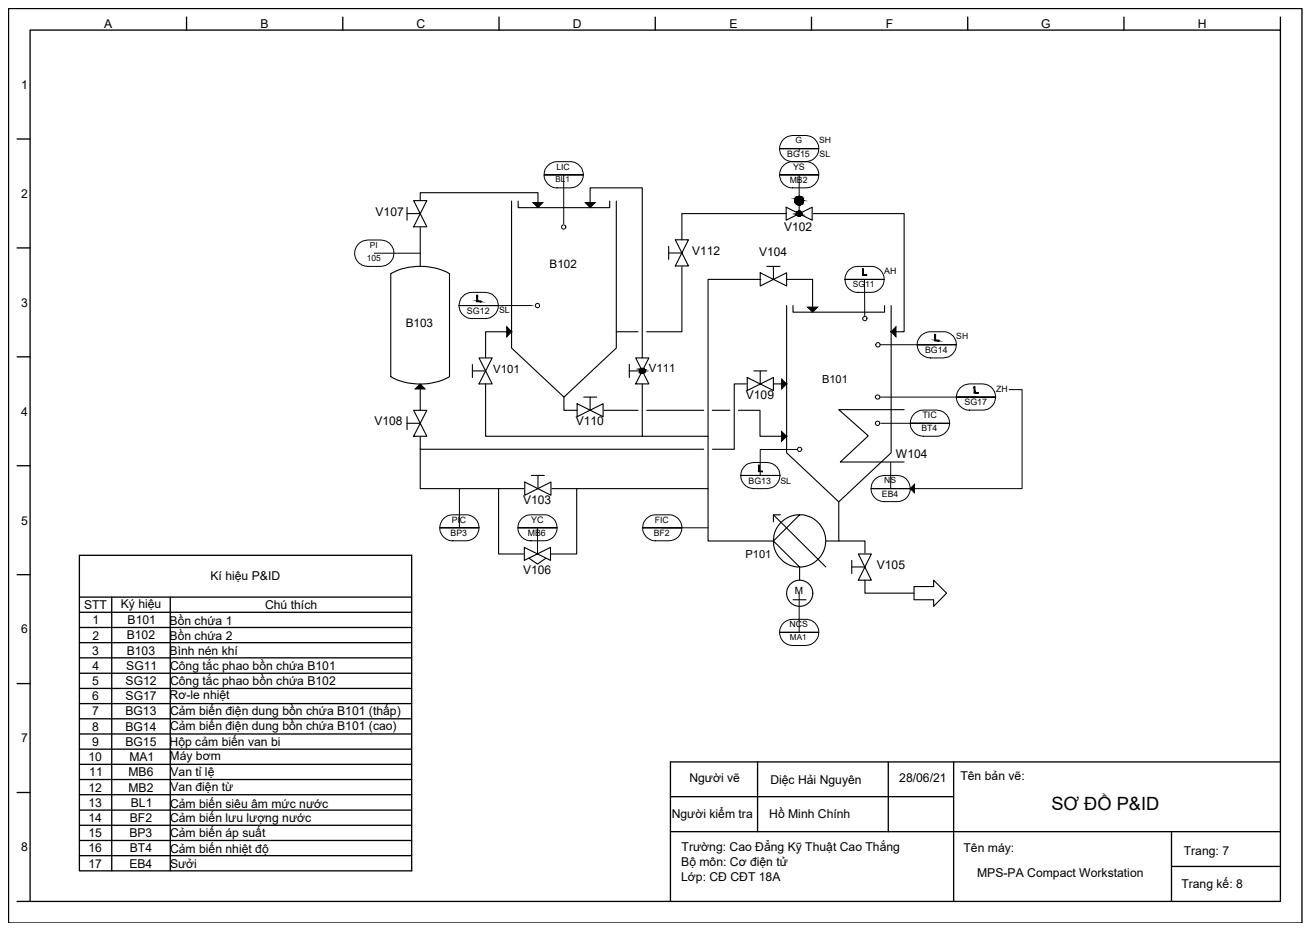
[picture p115: page 7]
Người vẽ; Diệc Hải Nguyên; Hồ Minh Chính; NCS MA1; Van tỉ lệ; Van điện từ; Cảm biến siêu âm mức nước; Tên máy:; Trang: 7

Kí hiệu P&ID

STT | Ký hiệu | Chú thích
1 | B101 | Bồn chứa 1
2 | B102 | Bồn chứa 2
3 | B103 | Bình nén khí
4 | SG11 | Công tắc phao bồn chứa B101
5 | SG12 | Công tắc phao bồn chứa B102
6 | SG17 | Rơ-le nhiệt
7 | BG13 | Cảm biến điện dung bồn chứa B101 (thấp)
8 | BG14 | Cảm biến điện dung bồn chứa B101 (cao)
9 | BG15 | Hộp cảm biến van bi
10 | MA1 | Máy bơm

Tên bản vẽ:

Người kiểm tra

14 | BF2 | Cảm biến lưu lượng nước
15 | BP3 | Cảm biến áp suất
16 | BT4 | Cảm biến nhiệt độ
17 | EB4 | Sưởi

Trường: Cao Đẳng Kỹ Thuật Cao Thắng
Bộ môn: Cơ điện tử
Lớp: CĐ CĐT 18A

Trang kế: 8 MPS-PA Compact Workstation

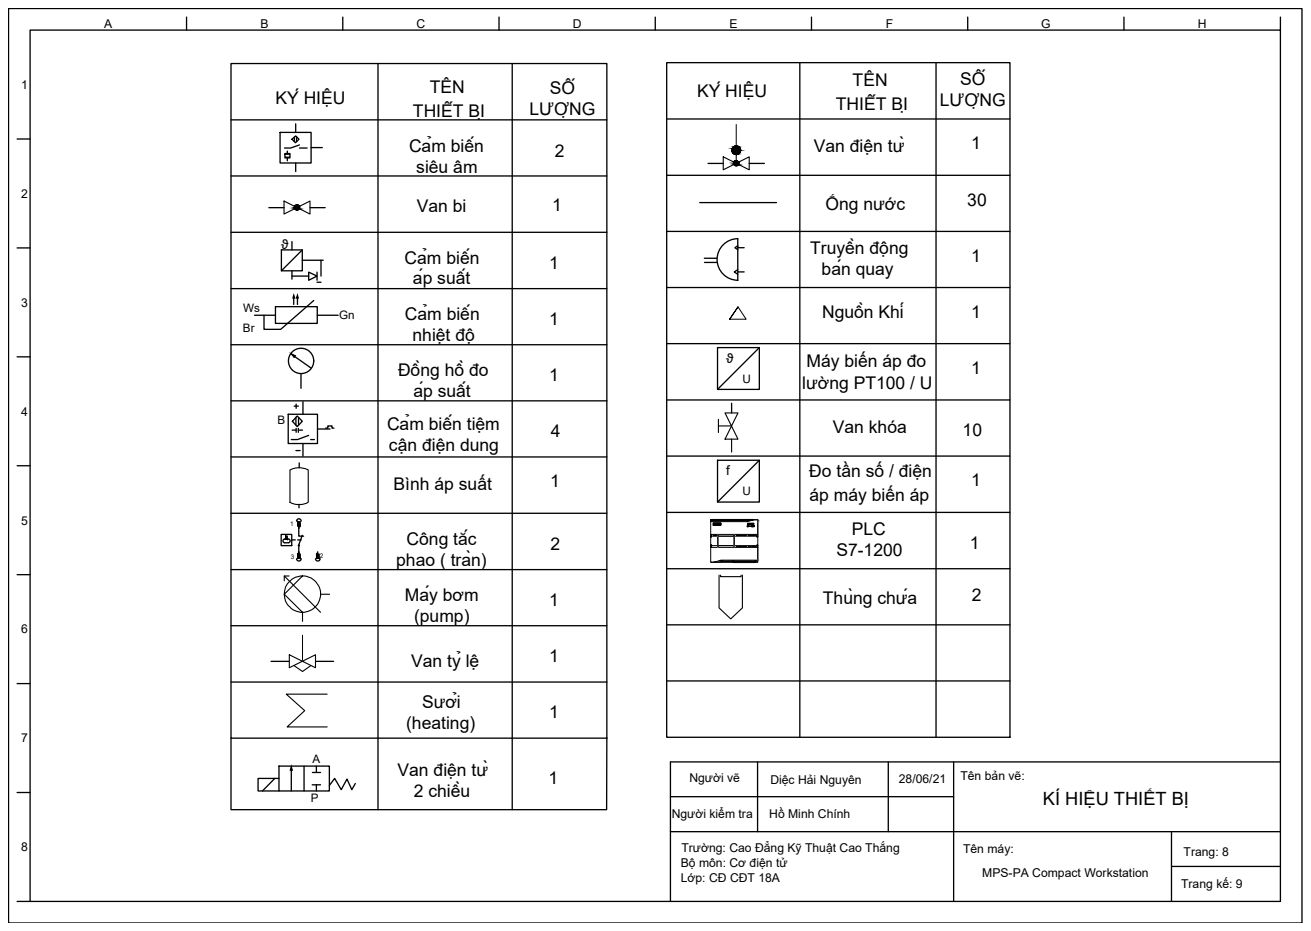
[picture p116: page 8]
Người vẽ; Diệc Hải Nguyên A; KÝ HIỆU; TÊN; THIẾT BỊ; Cảm biến siêu âm ϑ; Cảm biến áp suất; Cảm biến nhiệt độ; áp suất B; Cảm biến tiệm; Công tắc phao ( tràn); Máy bơm; LƯỢNG 2111421111; bán quay ϑ U; lường PT100 / U f U; LƯỢNG 111112 1; Van bi; Ống nước; Nguồn Khí 1; Van khóa; Tên máy:; Trang: 8; Trang kế: 9

Van điện từ

Truyền động

Máy biến áp đo

cận điện dung

Đo tần số / điện
áp máy biến áp

Bình áp suất

Thùng chứa

(pump) AP Van tỷ lệ

Sưởi (heating)

Van điện từ 2 chiều

28/06/21 | Tên bản vẽ: KÍ HIỆU THIẾT BỊ

Người kiểm tra | Hồ Minh Chính

Trường: Cao Đẳng Kỹ Thuật Cao Thắng
Bộ môn: Cơ điện tử
Lớp: CĐ CĐT 18A

MPS-PA Compact Workstation

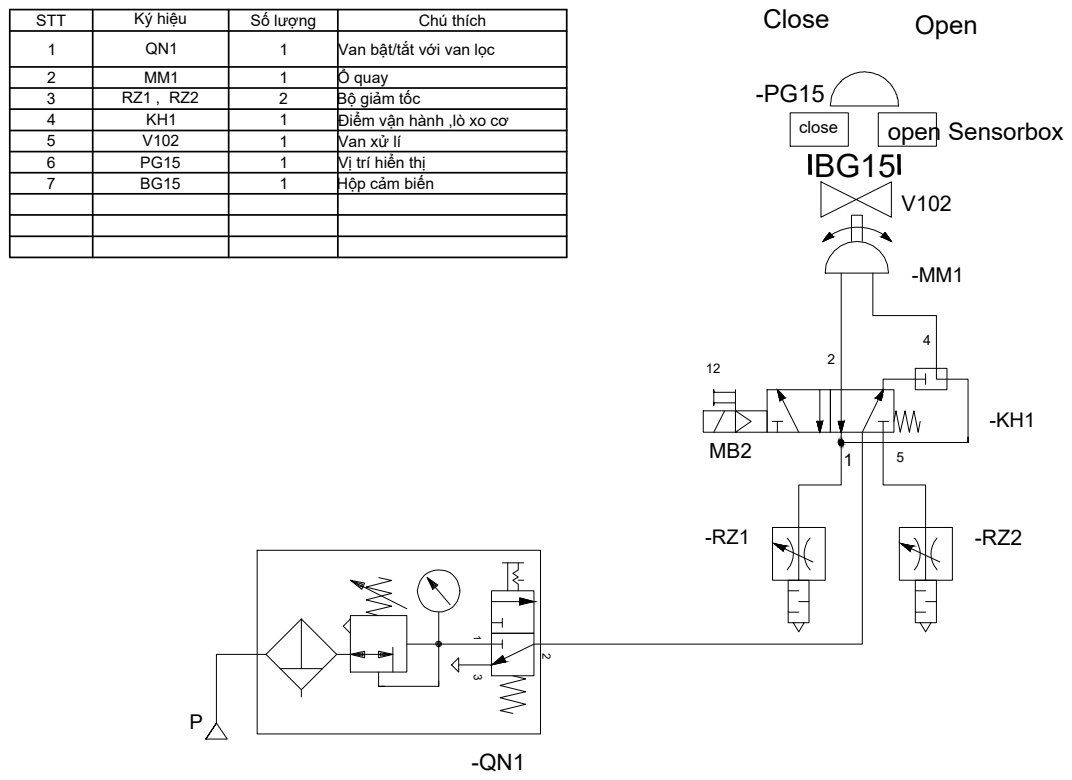
[picture p117: page 9]
close; open Sensorbox; Tên máy:; Trang: 9

STT | Ký hiệu | Số lượng | Chú thích

1 | QN1 | 1 | Van bật/tắt với van lọc

2 | MM1 | 1 | Ổ quay
3 | RZ1 , RZ2 | 2 | Bộ giảm tốc
4 | KH1 | 1 | Điểm vận hành ,lò xo cơ
5 | V102 | 1 | Van xử lí
6 | PG15 | 1 | Vị trí hiển thị
7 | BG15 | 1 | Hộp cảm biến

Người vẽ | Diệc Hải Nguyên | 28/06/21 | Tên bản vẽ: BẢN VẼ KHÍ NÉN

Người kiểm tra | Hồ Minh Chính

Trường: Cao Đẳng Kỹ Thuật Cao Thắng
Bộ môn: Cơ điện tử
Lớp: CĐ CĐT 18A

Trang kế: 10 MPS-PA Compact Workstation

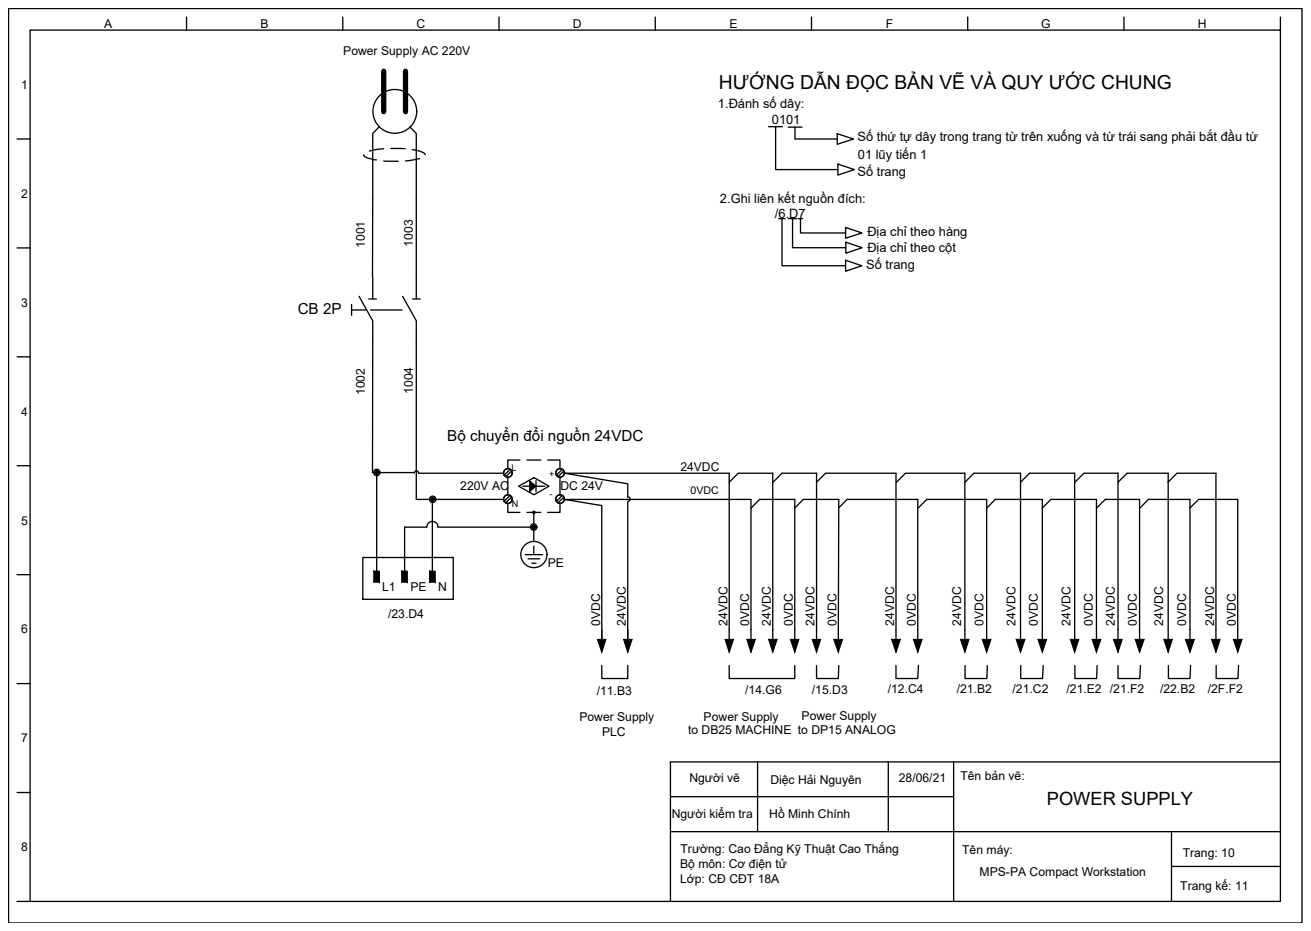
[picture p118: page 10]
Power Supply; Power Supply to DB25 MACHINE; to DP15 ANALOG 0VDC; 24VDC; 0VDC; Tên máy:; Trang: 10; Trang kế: 11; Số trang 1001 1002; /22.B2 24VDC; /2F.F2 24VDC

Power Supply AC 220V

HƯỚNG DẪN ĐỌC BẢN VẼ VÀ QUY ƯỚC CHUNG

1.Đánh số dây:

Số thứ tự dây trong trang từ trên xuống và từ trái sang phải bắt đầu từ
01 lũy tiến 1

2.Ghi liên kết nguồn đích:

Địa chỉ theo hàng
Địa chỉ theo cột
Số trang

MPS-PA Compact Workstation 1004

Bộ chuyển đổi nguồn 24VDC

Người vẽ | Diệc Hải Nguyên | 28/06/21 | Tên bản vẽ: POWER SUPPLY

Người kiểm tra | Hồ Minh Chính

Trường: Cao Đẳng Kỹ Thuật Cao Thắng
Bộ môn: Cơ điện tử
Lớp: CĐ CĐT 18A

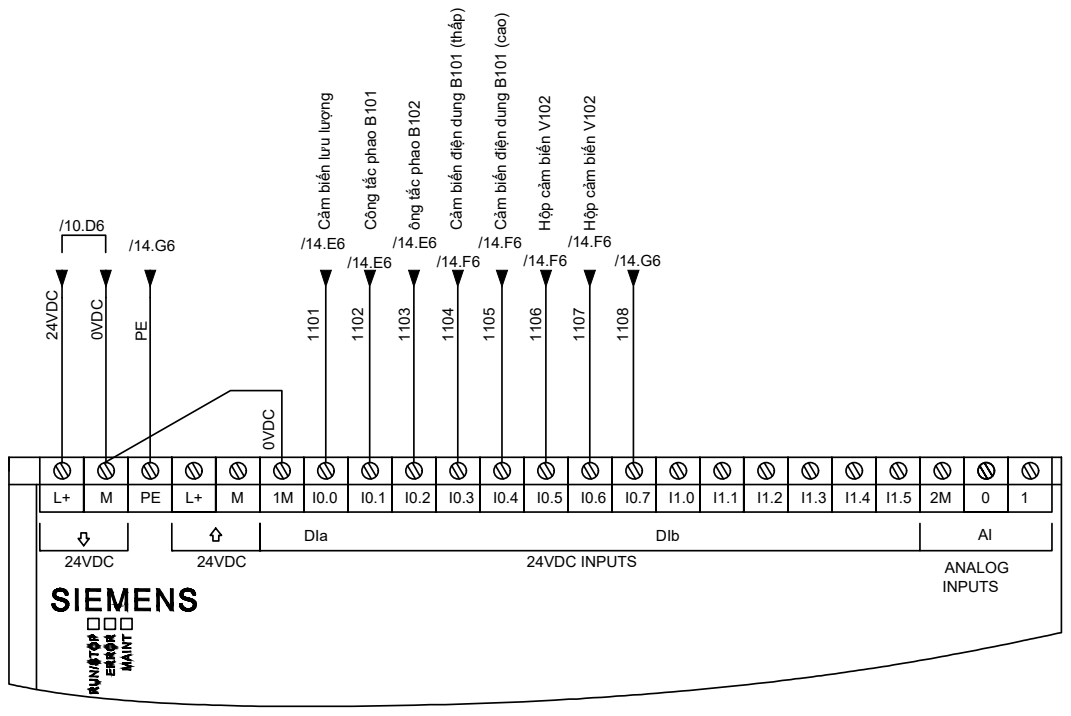
[picture p119: page 11]
24VDC INPUTS; 1 24VDC; 0VDC; Công tắc phao B101; ông tắc phao B102; Cảm biến điện dung B101 (thấp); Cảm biến điện dung B101 (cao); Hộp cảm biến V102; Tên máy:; Trang: 11; Trang kế: 12

Cảm biến lưu lượng

Hộp cảm biến V102

Người vẽ | Diệc Hải Nguyên | 28/06/21 | Tên bản vẽ: INPUTS PLC

Người kiểm tra | Hồ Minh Chính

Trường: Cao Đẳng Kỹ Thuật Cao Thắng
Bộ môn: Cơ điện tử
Lớp: CĐ CĐT 18A

MPS-PA Compact Workstation

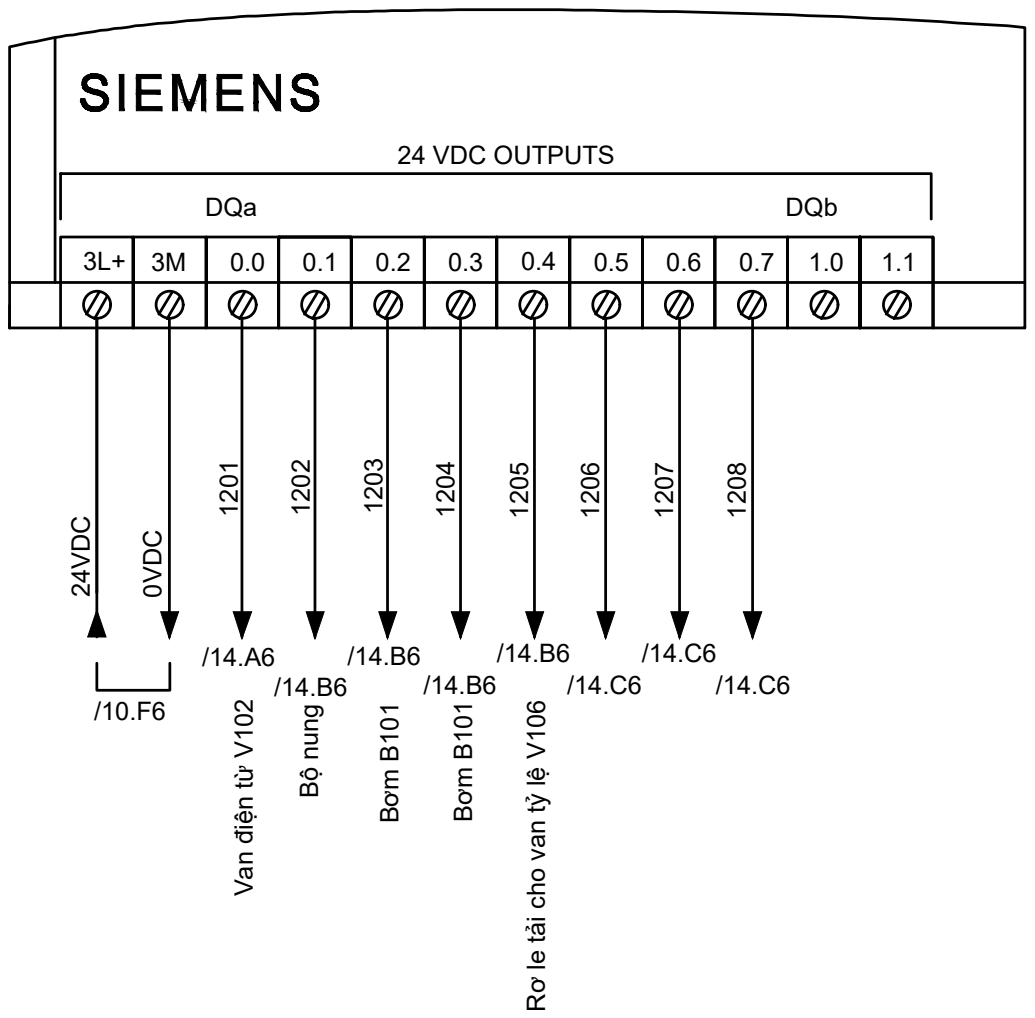
[picture p120: page 12]
24 VDC OUTPUTS; 1.1 24VDC; Van điện từ V102 0VDC; Bộ nung; Bơm B101; Rơ le tải cho van tỷ lệ V106 Bơm B101; Tên máy:; Trang: 12; Trang kế: 13

Người vẽ | Diệc Hải Nguyên | Tên bản vẽ: OUTPUTS PLC

Người kiểm tra | Hồ Minh Chính

Trường: Cao Đẳng Kỹ Thuật Cao Thắng
Bộ môn: Cơ điện tử
Lớp: CĐ CĐT 18A

MPS-PA Compact Workstation

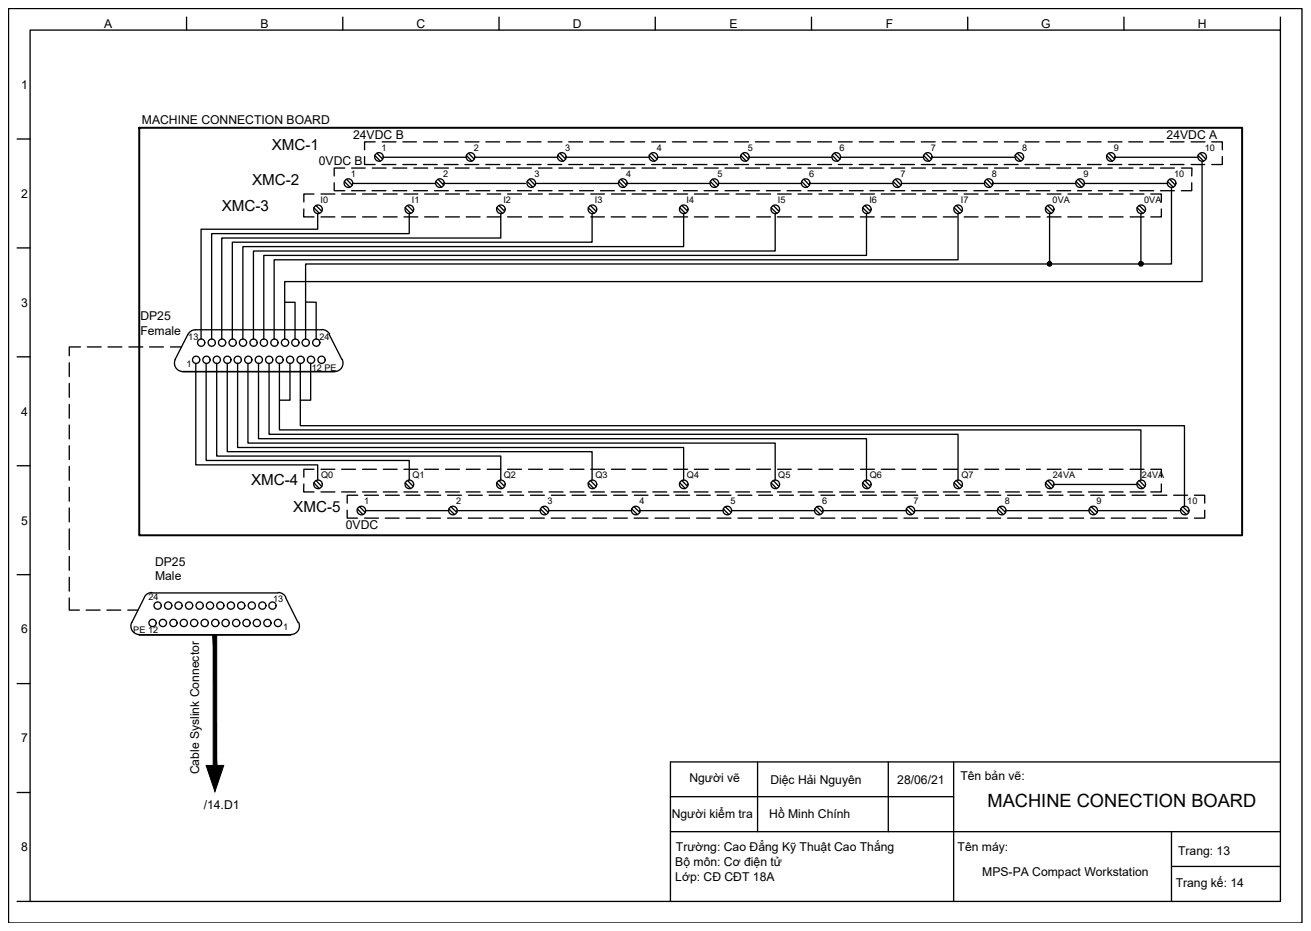
[picture p121: page 13]

Người vẽ | Diệc Hải Nguyên | 28/06/21 | Tên bản vẽ: MACHINE CONECTION BOARD

Người kiểm tra | Hồ Minh Chính

Trường: Cao Đẳng Kỹ Thuật Cao Thắng
Bộ môn: Cơ điện tử
Lớp: CĐ CĐT 18A

Trang kế: 14 MPS-PA Compact Workstation

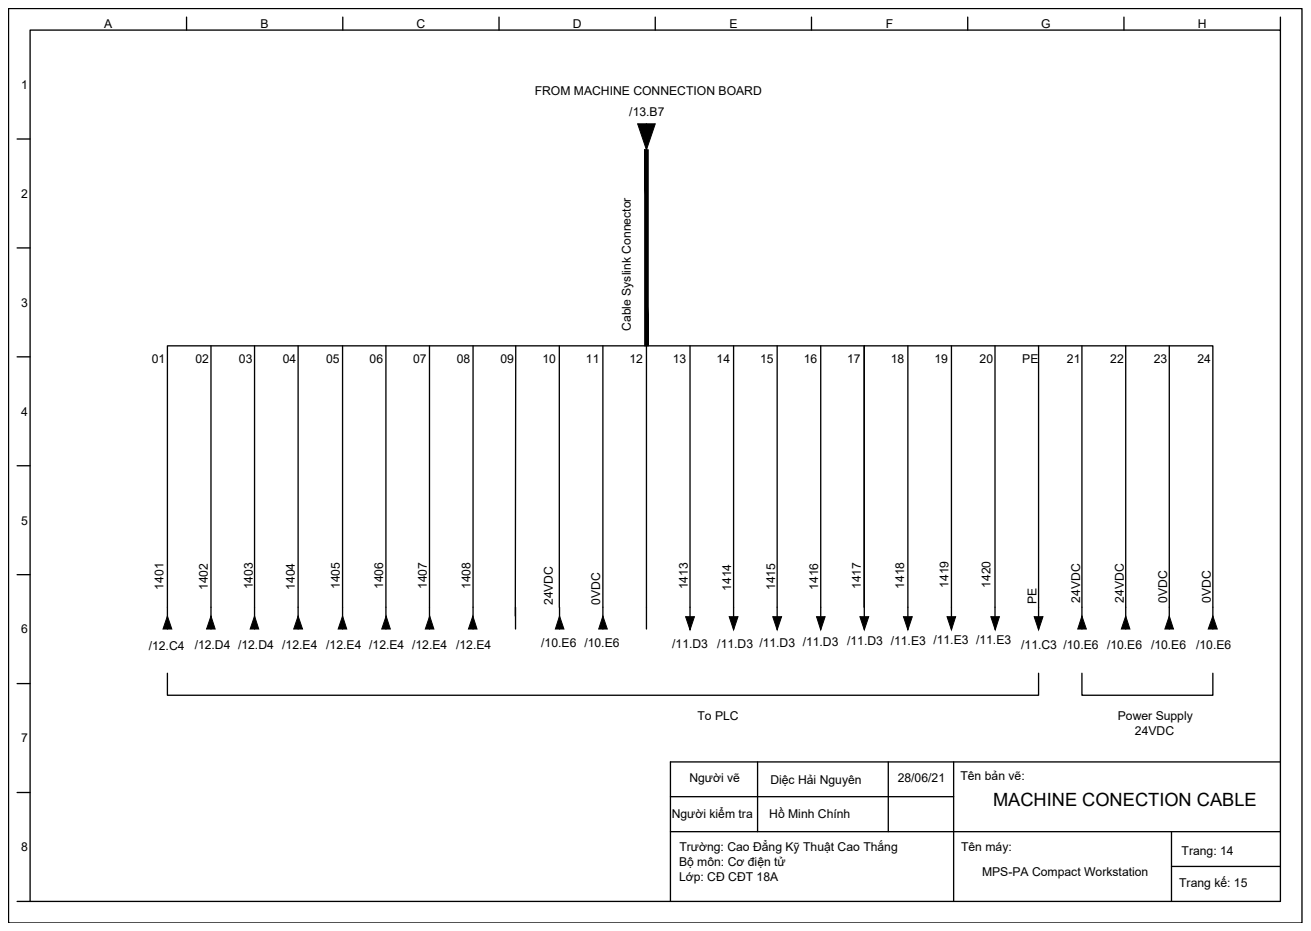
[picture p122: page 14]
To PLC; Power Supply; Tên máy:; Trang: 14; Trang kế: 15

FROM MACHINE CONNECTION BOARD /13.B7

Cable Syslink Connector | PE | 24VDC | 24VDC | 24VDC 0VDC 0VDC | 0VDC

MPS-PA Compact Workstation 24VDC

Người vẽ | Diệc Hải Nguyên | 28/06/21 | Tên bản vẽ: MACHINE CONECTION CABLE

Người kiểm tra | Hồ Minh Chính

Trường: Cao Đẳng Kỹ Thuật Cao Thắng
Bộ môn: Cơ điện tử
Lớp: CĐ CĐT 18A

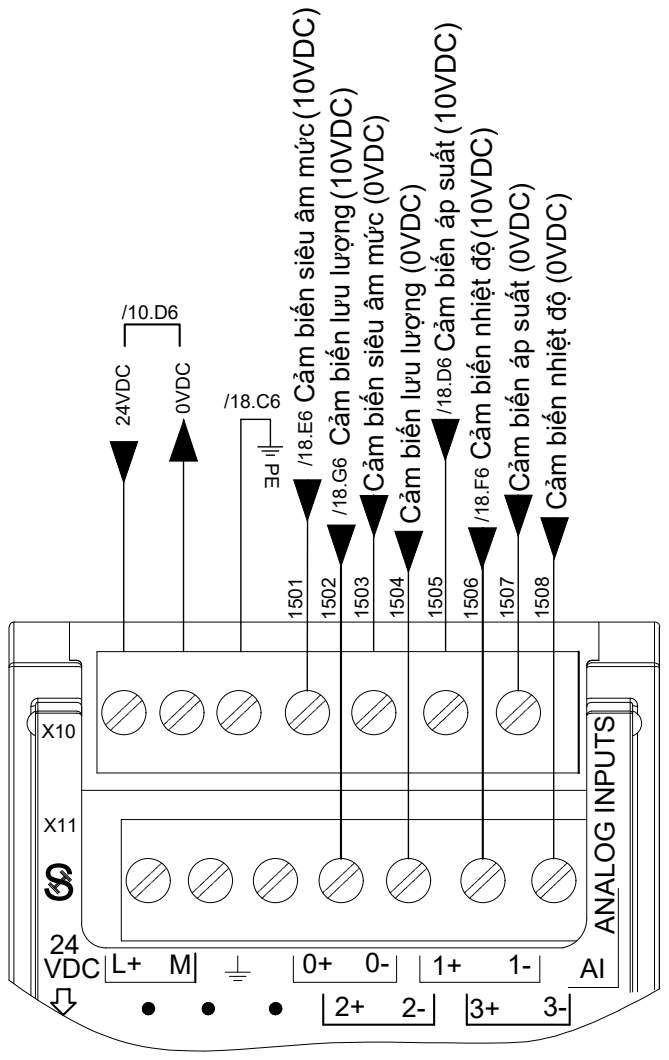
[picture p123: page 15]
Người vẽ; Diệc Hải Nguyên A; INPUTS ANALOG S; ANALOG INPUTS; Tên máy:; Trang: 15; /18.F6 (10VDC); (10VDC) (10VDC) (10VDC)

Cảm biến siêu âm mức

Cảm biến siêu âm mức (0VDC)

Cảm biến áp suất

Cảm biến lưu lượng

Cảm biến lưu lượng (0VDC)

Cảm biến áp suất (0VDC)

Cảm biến nhiệt độ (0VDC)

Cảm biến nhiệt độ

Trang kế: 16 PE

28/06/21 | Tên bản vẽ:

Người kiểm tra | Hồ Minh Chính

Trường: Cao Đẳng Kỹ Thuật Cao Thắng
Bộ môn: Cơ điện tử
Lớp: CĐ CĐT 18A

MPS-PA Compact Workstation

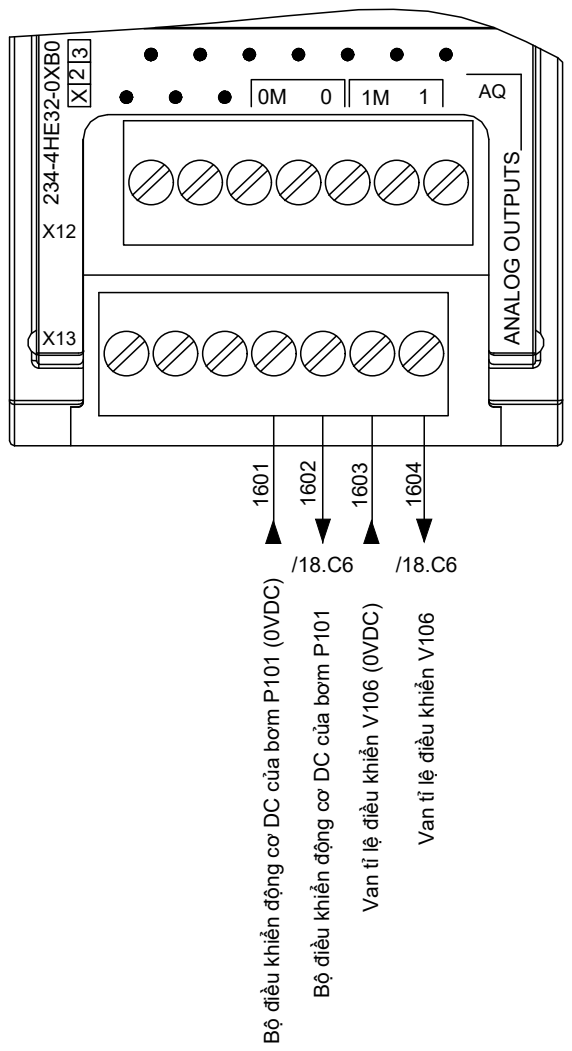
[picture p124: page 16]
Người vẽ; Diệc Hải Nguyên A; OUTPUTS ANALOG 234-4HE32-0XB0; ANALOG OUTPUTS; Tên máy:; Trang: 16; Trang kế: 17 1601

Bộ điều khiển động cơ DC của bơm P101 (0VDC)

Van tỉ lệ điều khiển V106 (0VDC)

Bộ điều khiển động cơ DC của bơm P101

Van tỉ lệ điều khiển V106

28/06/21 | Tên bản vẽ:

Người kiểm tra | Hồ Minh Chính

Trường: Cao Đẳng Kỹ Thuật Cao Thắng
Bộ môn: Cơ điện tử
Lớp: CĐ CĐT 18A

MPS-PA Compact Workstation

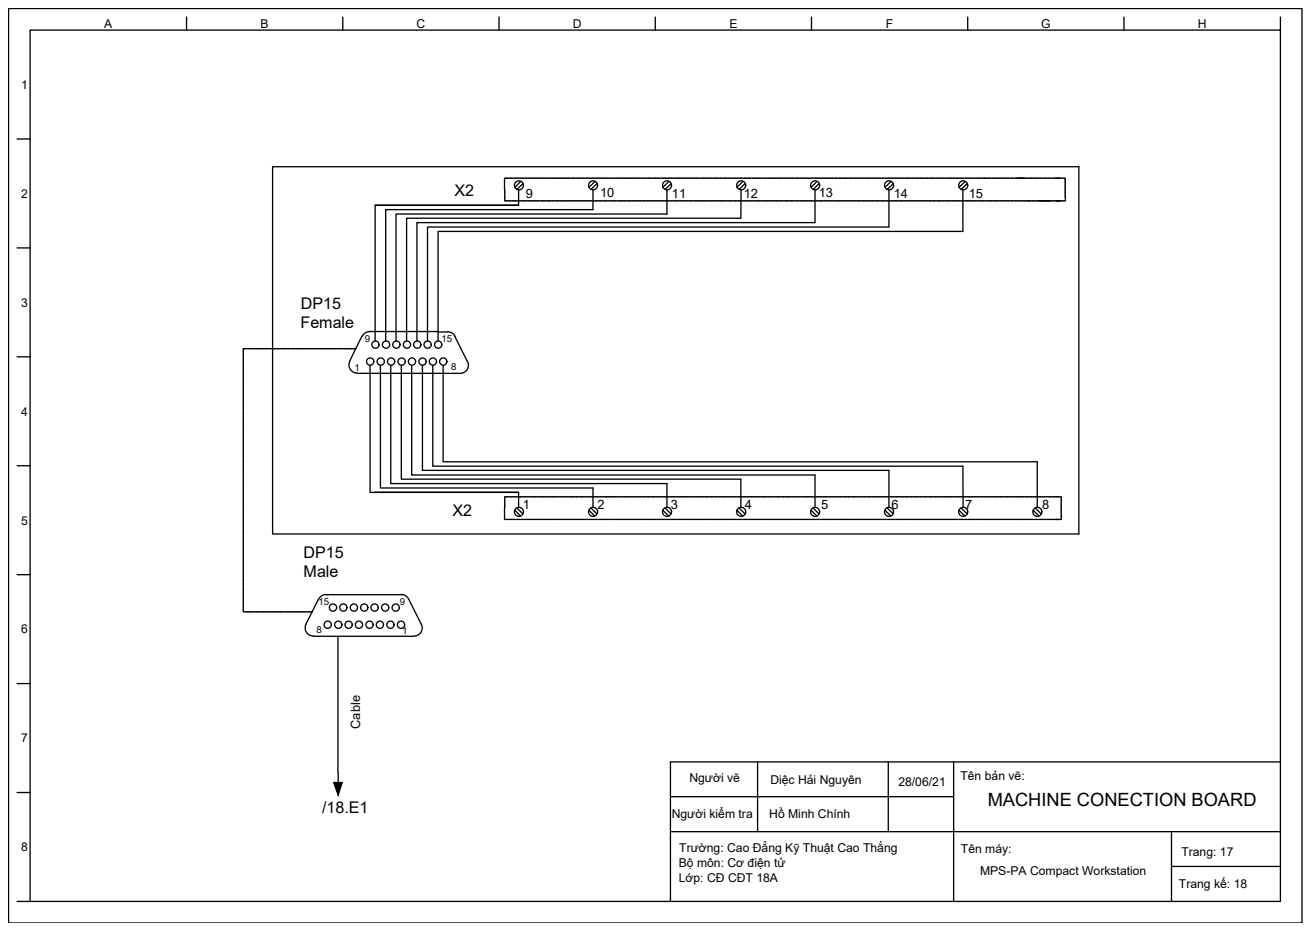
[picture p125: page 17]
8 Cable; MACHINE CONECTION BOARD; Tên máy:; Trang: 17

Người vẽ | Diệc Hải Nguyên | 28/06/21 | Tên bản vẽ:

Người kiểm tra | Hồ Minh Chính

Trường: Cao Đẳng Kỹ Thuật Cao Thắng
Bộ môn: Cơ điện tử
Lớp: CĐ CĐT 18A

Trang kế: 18 MPS-PA Compact Workstation

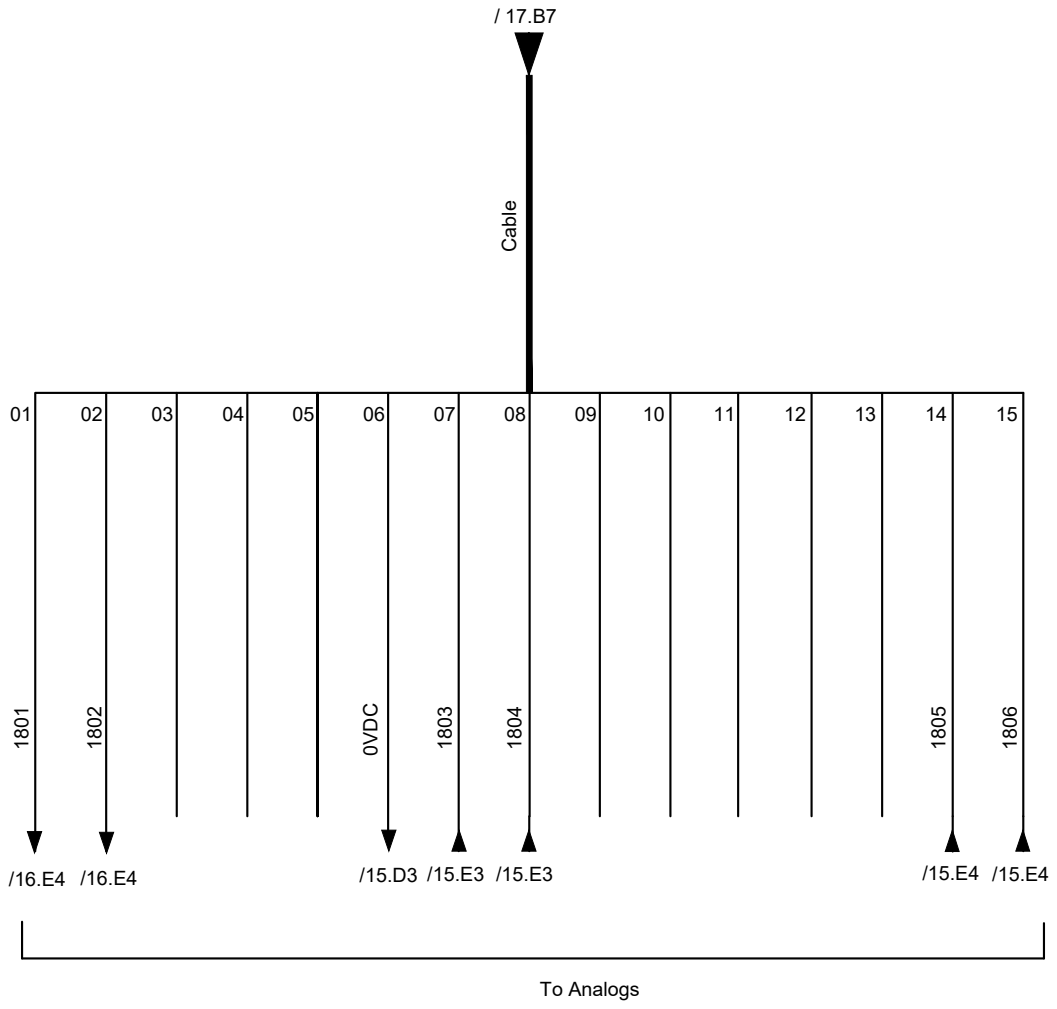
[picture p126: page 18]
Tên máy:; Trang: 18; Trang kế: 19 1801; 0VDC

To Analogs Cable

Người vẽ | Diệc Hải Nguyên | 28/06/21 | Tên bản vẽ: MACHINE CONECTION CABLE

Người kiểm tra | Hồ Minh Chính

Trường: Cao Đẳng Kỹ Thuật Cao Thắng
Bộ môn: Cơ điện tử
Lớp: CĐ CĐT 18A

MPS-PA Compact Workstation

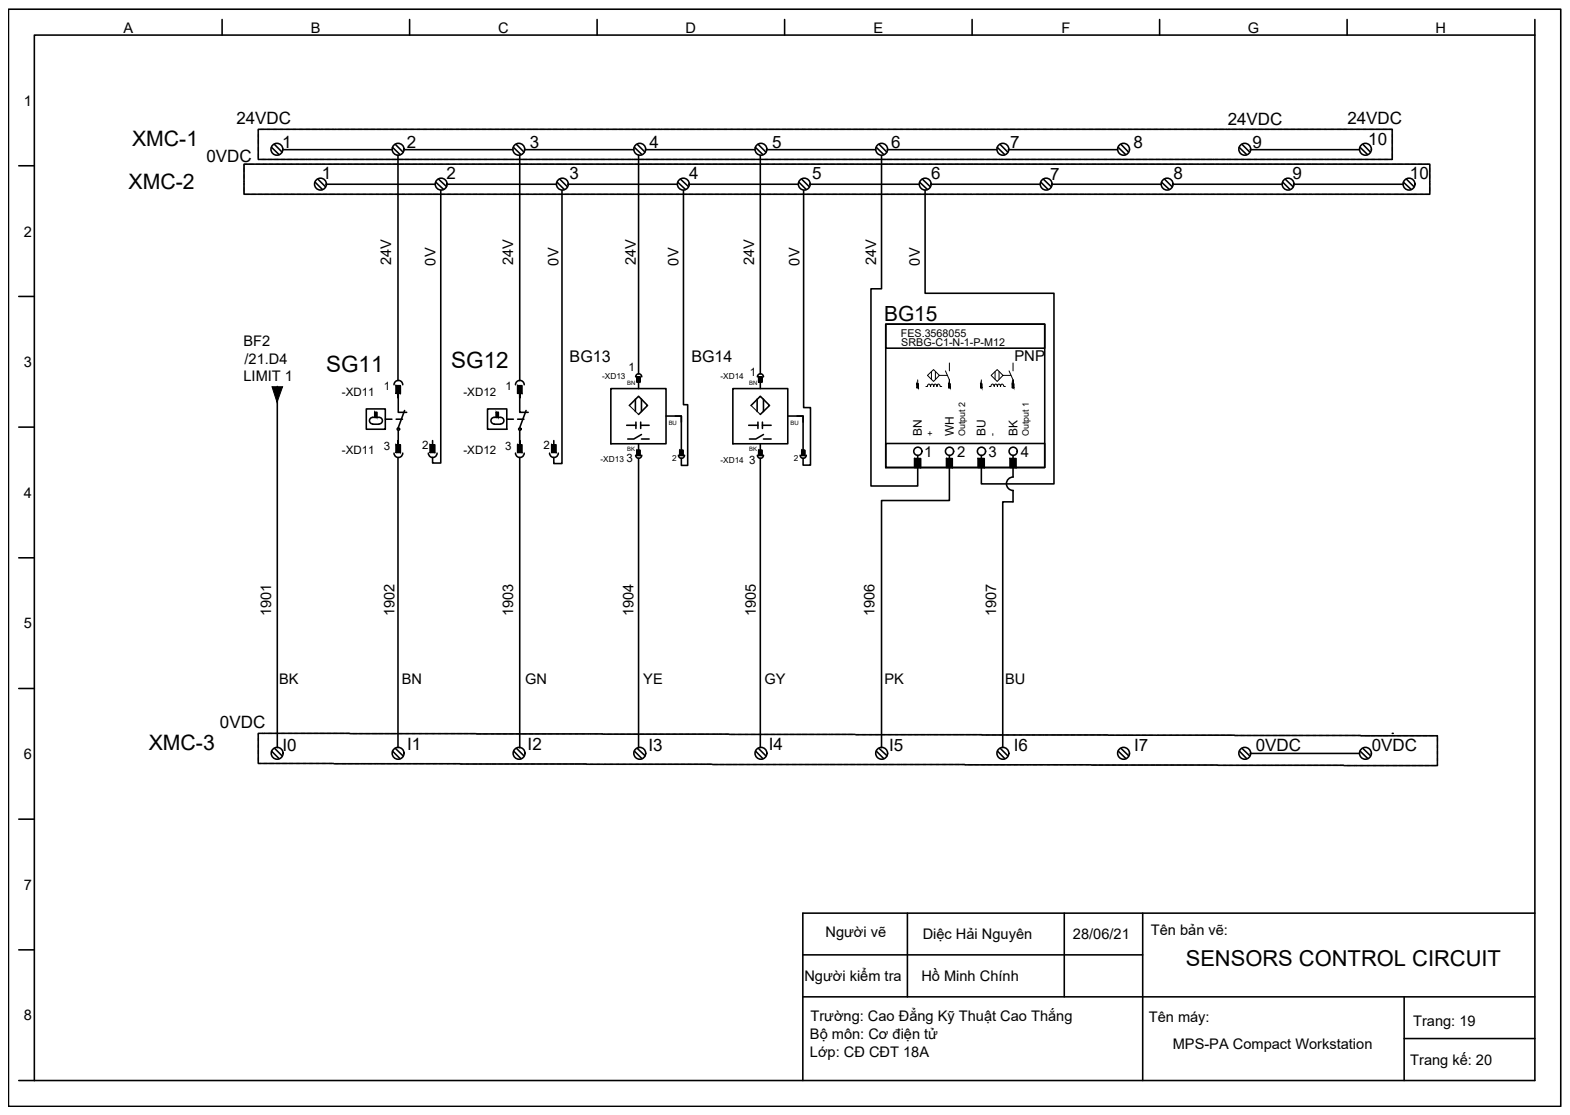
[picture p127: page 19]
-BKOutput 1; Tên máy:; Trang: 19; Trang kế: 20; LIMIT 1 1901

FES.3568055 SRBG-C1-N-1-P-M12 PNP

+WH Output 2 BU

Người vẽ | Diệc Hải Nguyên | 28/06/21 | Tên bản vẽ: SENSORS CONTROL CIRCUIT

Người kiểm tra | Hồ Minh Chính

Trường: Cao Đẳng Kỹ Thuật Cao Thắng
Bộ môn: Cơ điện tử
Lớp: CĐ CĐT 18A

MPS-PA Compact Workstation

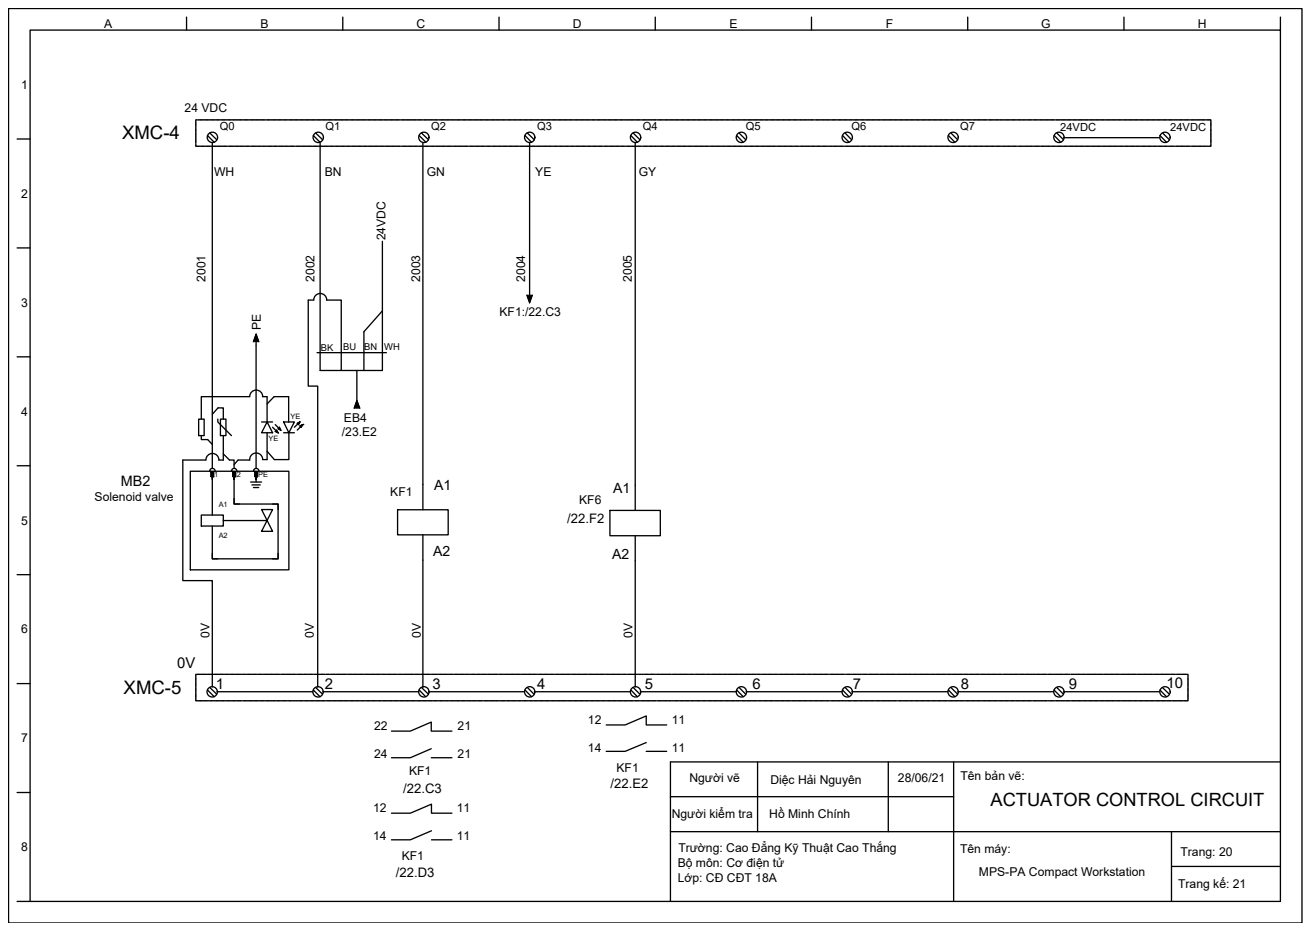
[picture p128: page 20]

ACTUATOR CONTROL CIRCUIT PE

Người vẽ | Diệc Hải Nguyên | 28/06/21 | Tên bản vẽ:

Người kiểm tra | Hồ Minh Chính

Trường: Cao Đẳng Kỹ Thuật Cao Thắng
Bộ môn: Cơ điện tử
Lớp: CĐ CĐT 18A

MPS-PA Compact Workstation

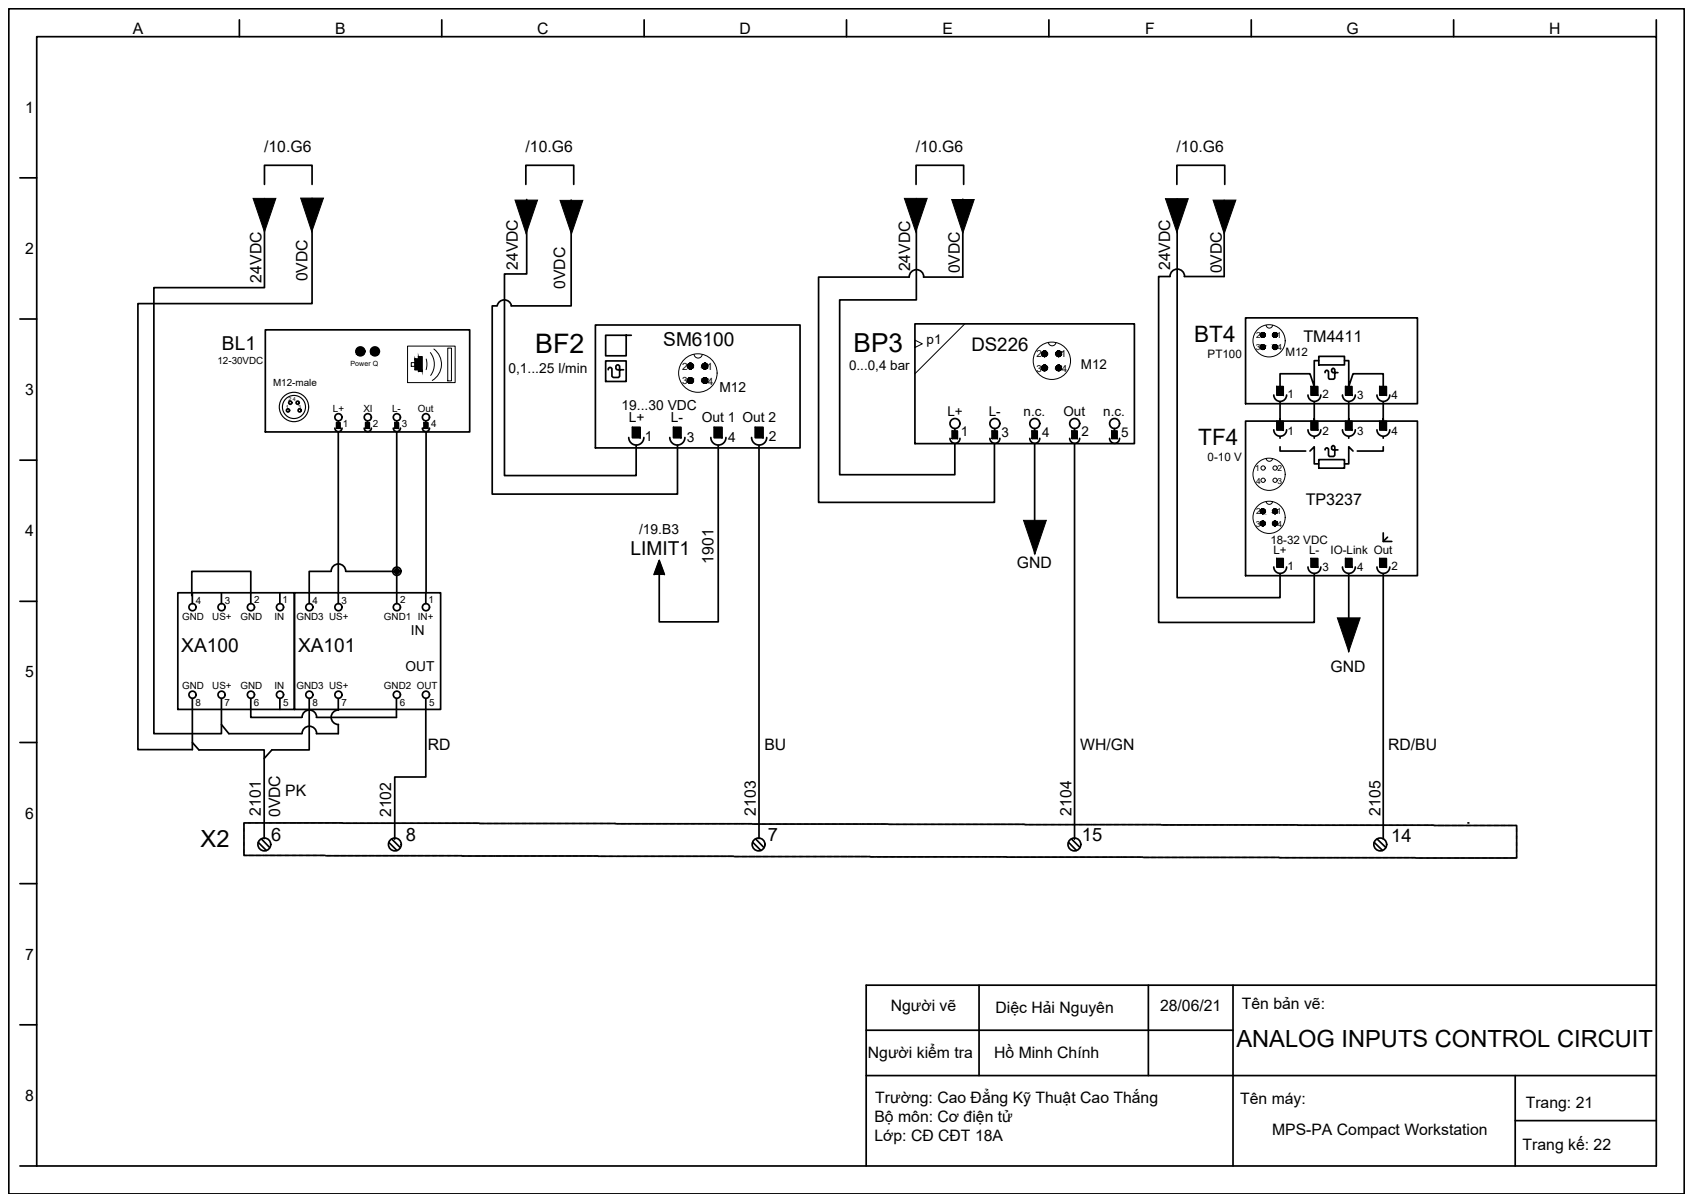
[picture p129: page 21]
L-3 Out4; Power Q; 0,1...25 l/min; 3 19...30 VDC; 0...0,4 bar Out 2; 2 M12 Out 1; n.c.4 Out2; 4 18-32 VDC; IO-Link4 Out2; Tên máy:; Trang: 21; Trang kế: 22 2101; 2105 1901 24VDC; 0VDC; 24VDC; /10.G6 0VDCPK

4 US+ 3 XA100 GND GND IN GND 8 US+ 7 GND IN | GND3 | 4 US+ 3 XA101 GND1 IN+ INOUT 8 US+ GND2 6 OUT

Người vẽ | Diệc Hải Nguyên | 28/06/21 | Tên bản vẽ: ANALOG INPUTS CONTROL CIRCUIT

Người kiểm tra | Hồ Minh Chính

Trường: Cao Đẳng Kỹ Thuật Cao Thắng
Bộ môn: Cơ điện tử
Lớp: CĐ CĐT 18A

MPS-PA Compact Workstation

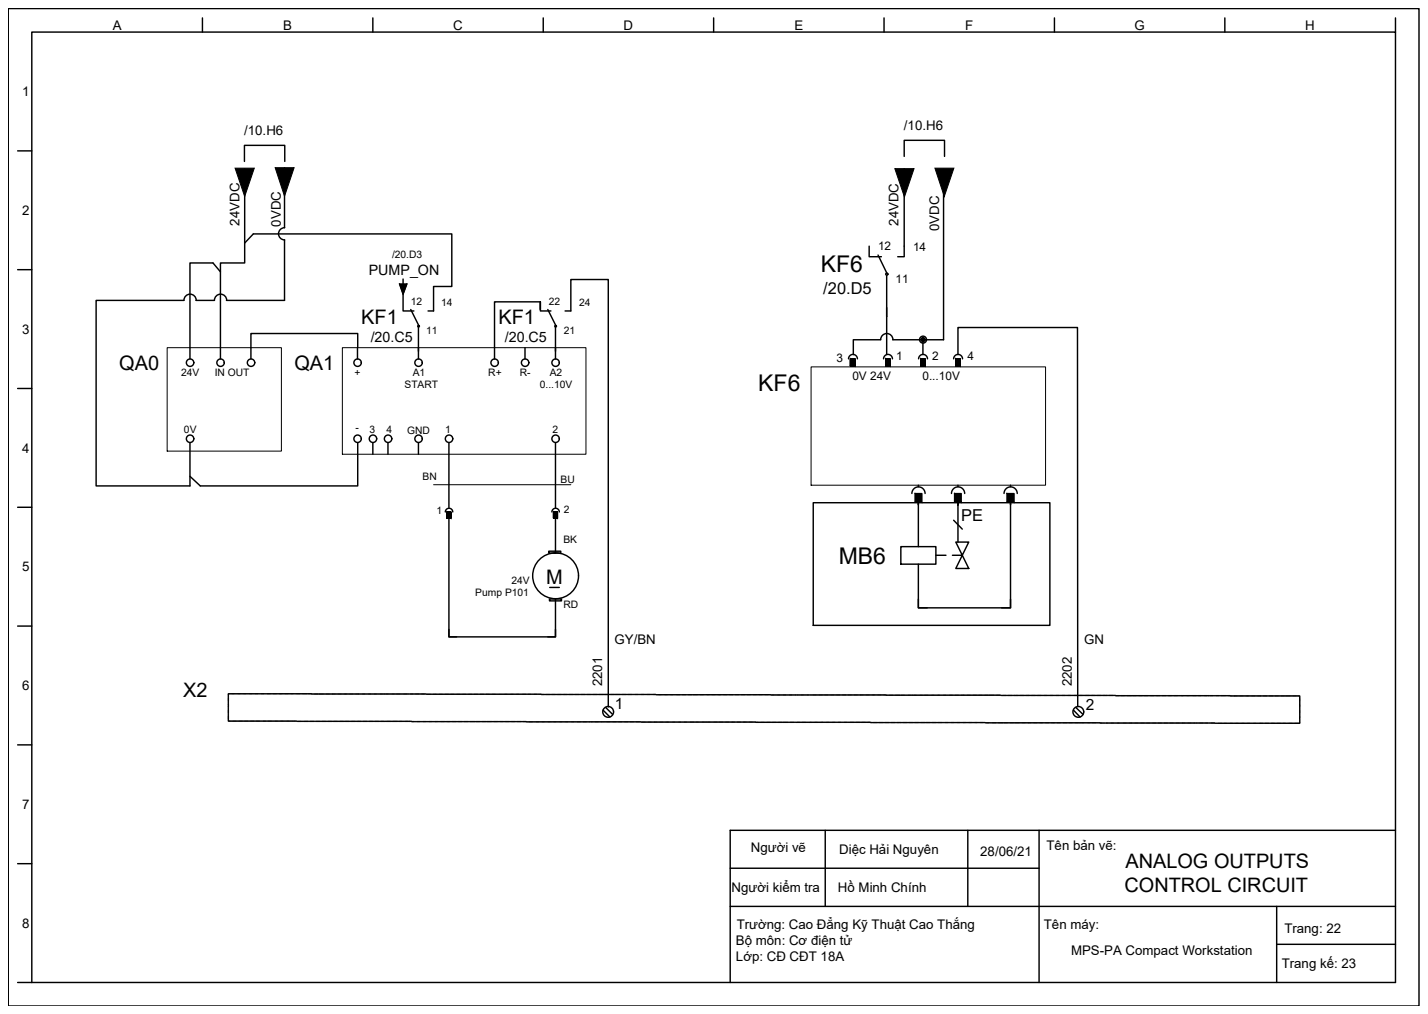
[picture p130: page 22]
IN OUT; A1 START GND; Pump P101; Tên máy:; Trang: 22; Trang kế: 23; 2202 24VDC; 0VDC; 24VDC

Người vẽ | Diệc Hải Nguyên | 28/06/21 | Tên bản vẽ: ANALOG OUTPUTS CONTROL CIRCUIT

Người kiểm tra | Hồ Minh Chính

Trường: Cao Đẳng Kỹ Thuật Cao Thắng
Bộ môn: Cơ điện tử
Lớp: CĐ CĐT 18A

MPS-PA Compact Workstation

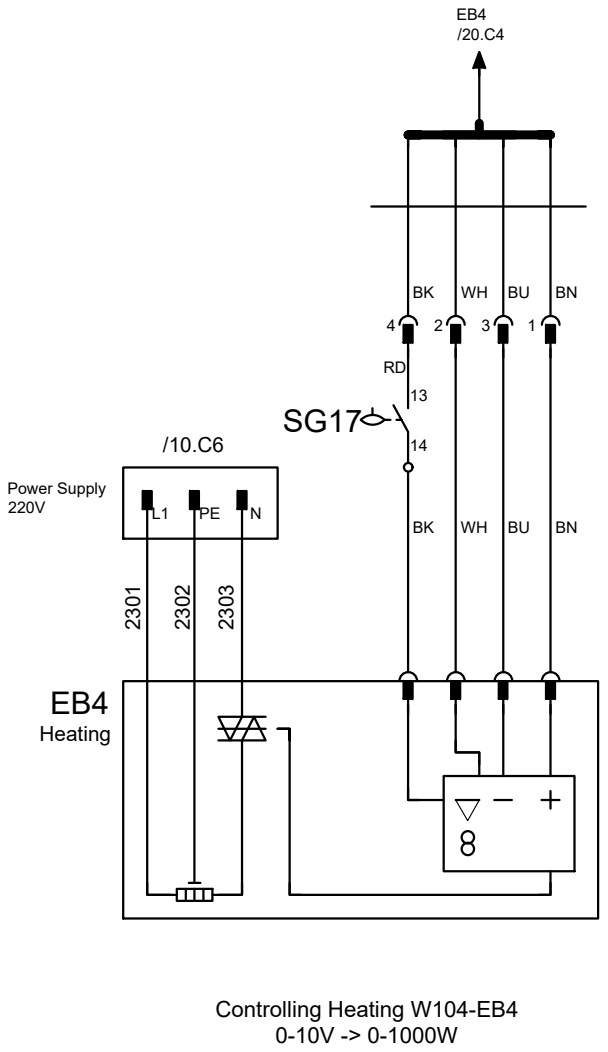
[picture p131: page 23]
Power Supply 220V; Controlling Heating W104-EB4 0-10V -> 0-1000W; Tên máy:; Trang: 23

Người vẽ | Diệc Hải Nguyên | 28/06/21 | Tên bản vẽ: HEATING/COOLING

Người kiểm tra | Hồ Minh Chính

Trường: Cao Đẳng Kỹ Thuật Cao Thắng
Bộ môn: Cơ điện tử
Lớp: CĐ CĐT 18A

MPS-PA Compact Workstation

Trang kế: End
