anhembedded/PCS_HMI/Doc/bv h.Anh/ban dien/2d/PDF/1.PDF

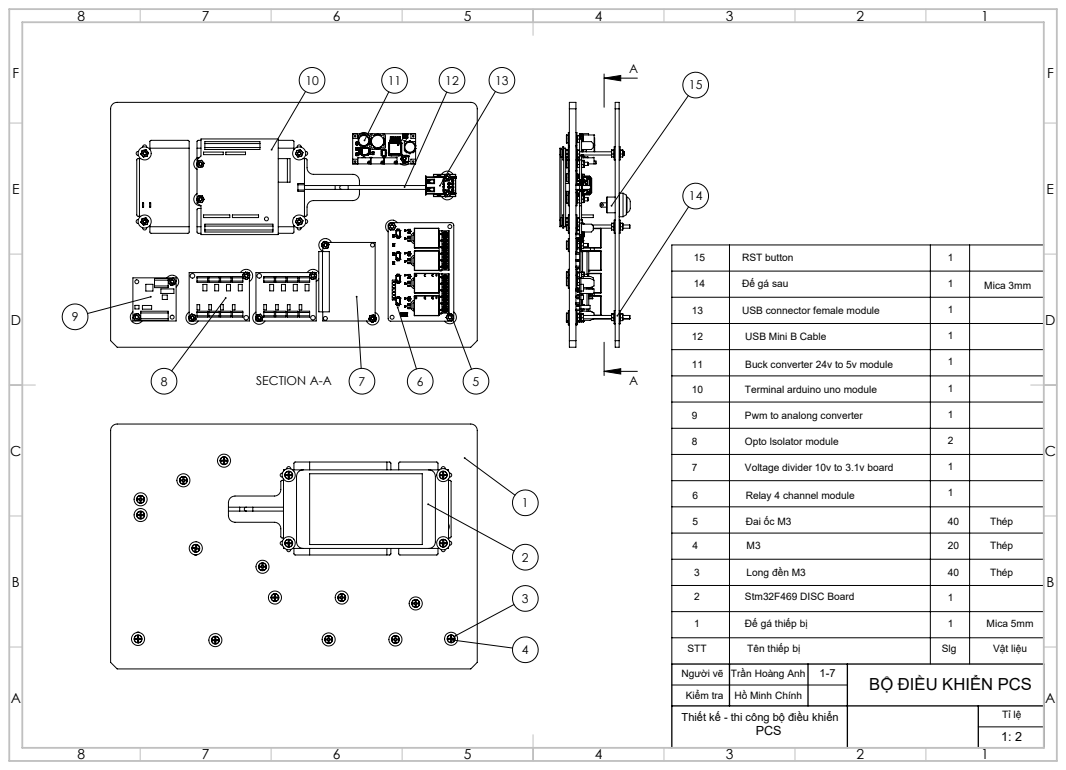
[picture p132: page 1]
SECTION A-A

15 | RST button | 1

14 | Đế gá sau | 1 | Mica 3mm
13 | USB connector female module | 1
12 | USB Mini B Cable | 1
11 | Buck converter 24v to 5v module | 1
10 | Terminal arduino uno module | 1
9 | Pwm to analong converter | 1
8 | Opto lsolator module | 2
7 | Voltage divider 10v to 3.1v board | 1
6 | Relay 4 channel module | 1

5 | Đai ốc M3 | 40 | Thép
4 | M3 | 20 | Thép

3 | Long đền M3 | 40 | Thép
2 | Stm32F469 DISC Board | 1

1 | Đế gá thiếp bị | 1 | Mica 5mm
STT | Tên thiếp bị | Slg | Vật liệu
Người vẽ | Trần Hoàng Anh | 1-7 | BỘ ĐIỀU KHIỂN PCS
Kiểm tra | Hồ Minh Chính
Thiết kế - thi công bộ điều khiển PCS | | Tỉ lệ
