anhembedded/PCS_HMI/Doc/bv h.Anh/ban dien/2d/PDF/4.PDF

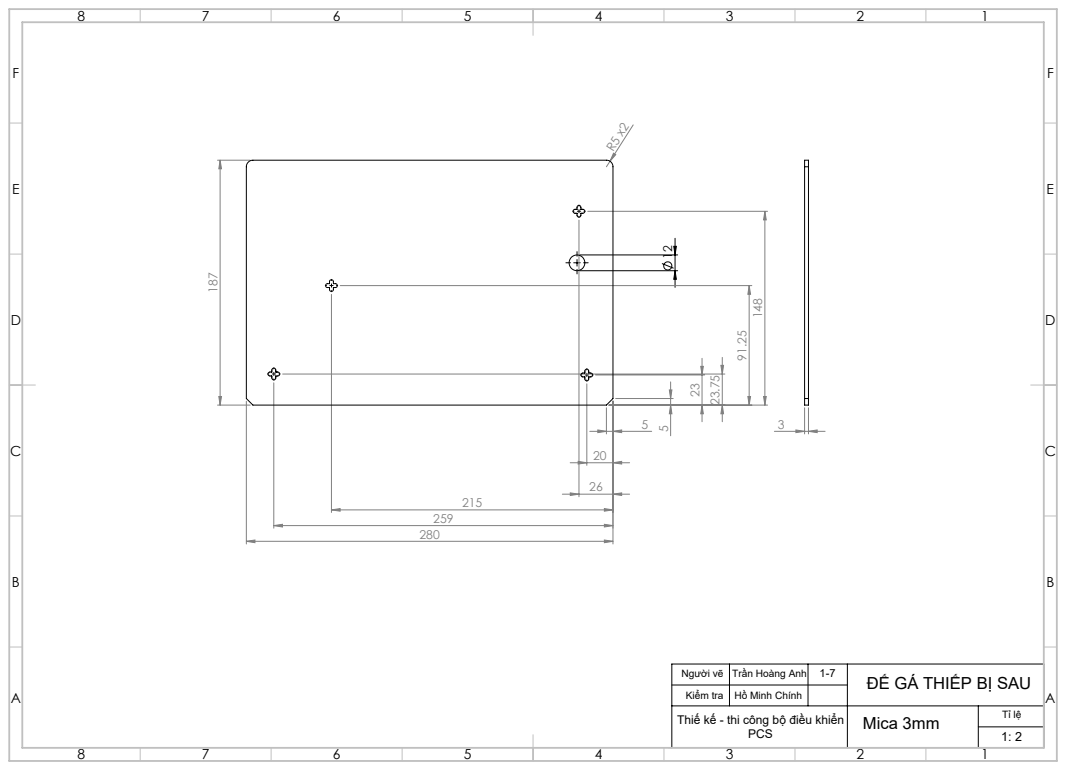
[picture p134: page 1]

Người vẽ | Trần Hoàng Anh | 1-7 | ĐẾ GÁ THIẾP BỊ SAU
Kiểm tra | Hồ Minh Chính
Thiế kế - thi công bộ điều khiển | Mica 3mm | Tỉ lệ

PCS | | 1: 2
