anhembedded/PCS_HMI/Doc/bv h.Anh/ban dien/2d/PDF/BIA.PDF

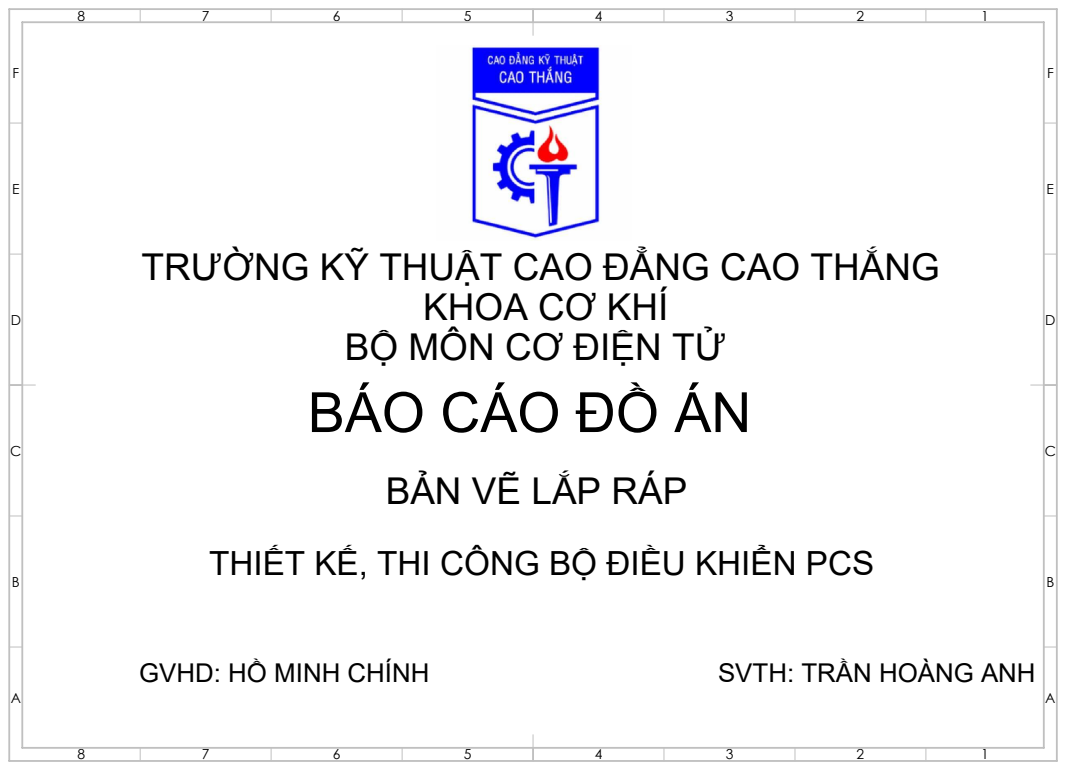
[picture p147: page 1]

TRƯỜNG KỸ THUẬT CAO ĐẲNG CAO THẮNG
BÁO CÁO ĐỒ ÁN
BẢN VẼ LẮP RÁP

KHOA CƠ KHÍ
BỘ MÔN CƠ ĐIỆN TỬ

THIẾT KẾ, THI CÔNG BỘ ĐIỀU KHIỂN PCS

GVHD: HỒ MINH CHÍNH

SVTH: TRẦN HOÀNG ANH
