anhembedded/PCS_HMI/Test/Core/u_task/Inc/u_appUtilities.h

#ifndef AC98AEF3_6C0F_4E6D_936D_C090A273E1CD
#define AC98AEF3_6C0F_4E6D_936D_C090A273E1CD
#include "u_appMain.h"

portBASE_TYPE isTaskSuspended(xTaskHandle taskHandle);
portBASE_TYPE isTaskRunOrReady(xTaskHandle taskHandle);


#endif /* AC98AEF3_6C0F_4E6D_936D_C090A273E1CD */
