anhembedded/PCS_HMI/Test/Core/u_driver/inc/u_rcc.h

#ifndef CORE_U_DRIVER_U_RCC
#define CORE_U_DRIVER_U_RCC

#include "stm32f4xx.h"

void u_rcc_enableClk_ADC1();
void u_rcc_enableClk_GPIOA();
void u_rcc_enableClk_GPIOB();
void u_rcc_enableClk_GPIOC();
void u_rcc_enableClk_GPIOD();
void u_rcc_enableClk_GPIOG();
void u_rcc_enableClk_GPIOH();
void u_rcc_enableClk_GPIOK();
void u_rcc_enableClk_TIM5();

#endif /* CORE_U_DRIVER_U_RCC */
